rickcox/Hepta-Pi/3V3_to_2v5_PSU.kicad_sch

## KiCad design 3V3_to_2v5_PSU.kicad_sch (2023-05-14)

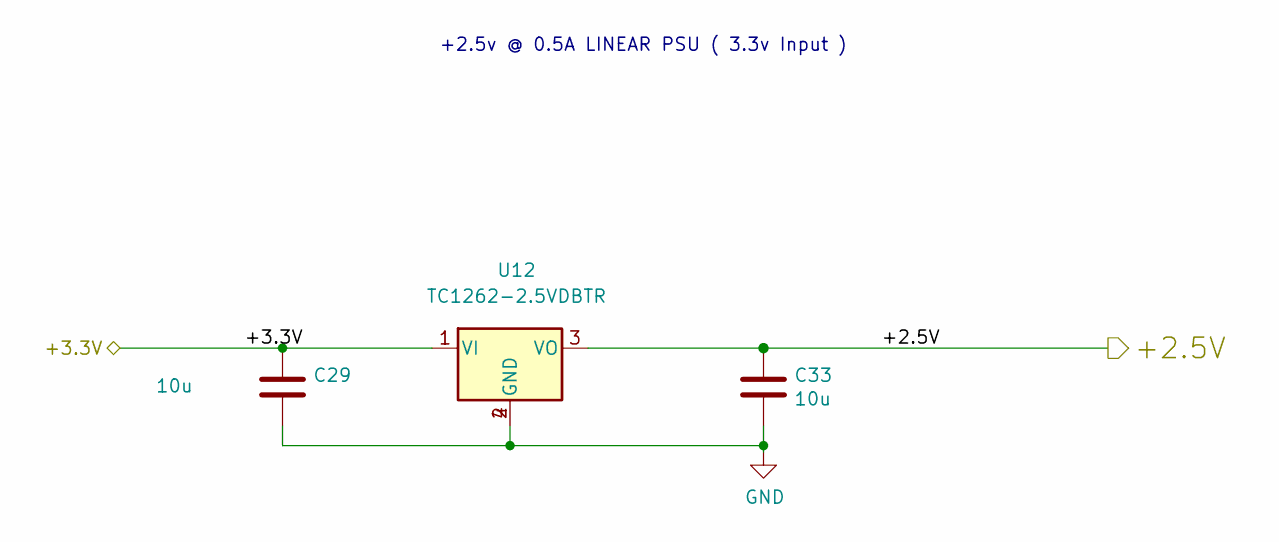
[picture p10: schematic 3V3_to_2v5_PSU.kicad_sch]

Parts:
C29, C33: 10u; C_0603_1608Metric; Part Description CAP CER 10UF 6.3V X5R 0603; LCSC Part Number C19702
U12: TC1262-2.5VDBTR; SOT-223; Manuf Partno TC1262-2.5VDBTR; LCSC Part Number C233212

Connections:
+2.5V: C33.1, U12.3 (VO)
+3.3V: C29.1, U12.1 (VI)
GND: C29.2, C33.2, U12.2 (GND), U12.4

Notes on the sheet:
+2.5v @ 0.5A LINEAR PSU ( 3.3v Input )
