rickcox/Hepta-Pi/12V_to_1v0_PSU.kicad_sch

## KiCad design 12V_to_1v0_PSU.kicad_sch (2023-05-14)

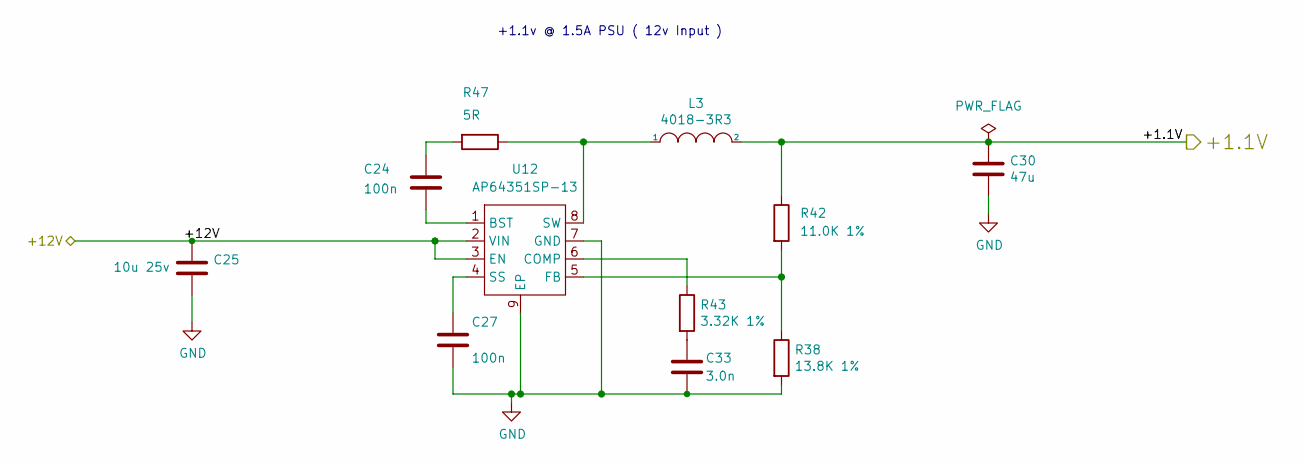
[picture p11: schematic 12V_to_1v0_PSU.kicad_sch]

Parts:
C24, C27: 100n; C_0402_1005Metric; LCSC Part Number C1525
C25: 10u 25v; C_0805_2012Metric; LCSC Part Number C440198
C30: 47u; C_1206_3216Metric; LCSC Part Number C96123
C33: 3.0n; C_0603_1608Metric; LCSC Part Number C1613
L3: 4018-3R3; L_Bourns-SRN4018; LCSC Part Number C307830
R38: 13.8K 1%; R_0603_1608Metric; LCSC Part Number C862888
R42: 11.0K 1%; R_0603_1608Metric; LCSC Part Number C25950
R43: 3.32K 1%; R_0603_1608Metric; LCSC Part Number C22995
R47: 5R; R_0603_1608Metric; LCSC Part Number C25197
U12: AP64351SP-13; SOIC-8-1EP_3.9x4.9mm_P1.27mm_EP2.95x4.9mm_Mask2.71x3.4mm

Connections:
+1.1V: C30.1, L3.2, R42.1
+12V: C25.1, U12.2 (VIN), U12.3 (EN)
GND: C25.2, C27.2, C30.2, C33.2, R38.2, U12.7 (GND), U12.9 (EP)
unnamed: C24.1, R47.2
unnamed: C24.2, U12.1 (BST)
unnamed: C27.1, U12.4 (SS)
unnamed: C33.1, R43.2
unnamed: L3.1, R47.1, U12.8 (SW)
unnamed: R38.1, R42.2, U12.5 (FB)
unnamed: R43.1, U12.6 (COMP)

Notes on the sheet:
+1.1v @ 1.5A PSU ( 12v Input )
