rickcox/Hepta-Pi/12V_to_1v2_PSU.kicad_sch

## KiCad design 12V_to_1v2_PSU.kicad_sch (2023-05-14)

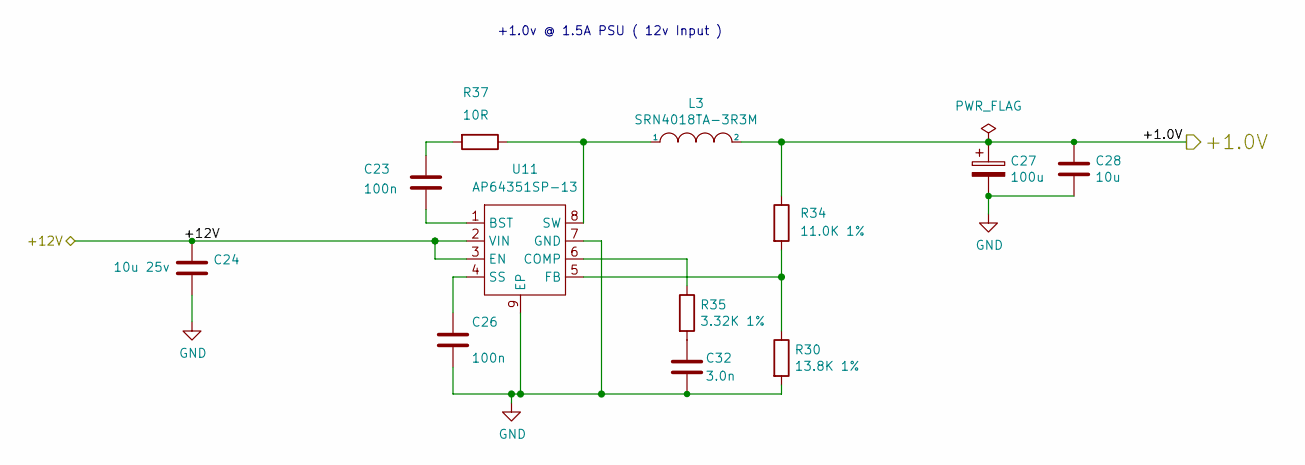
[picture p12: schematic 12V_to_1v2_PSU.kicad_sch]

Parts:
C23, C26: 100n; C_0402_1005Metric; Part Description CAP CER 0.1UF 6.3V X5R 0603; LCSC Part Number C1525
C24: 10u 25v; C_0805_2012Metric; Part Description CAP CER 10UF 25V X5R 0805; LCSC Part Number C440198
C27: 100u; CP_EIA-3528-21_Kemet-B; Part Description CAP TANT 100UF 10% 10V 2917; LCSC Part Number C16133
C28: 10u; C_0603_1608Metric; Part Description CAP CER 10UF 6.3V X5R 0603; LCSC Part Number C19702
C32: 3.0n; C_0603_1608Metric; Part Description CAP CER 0603 3NF 16V; LCSC Part Number C1613
L3: SRN4018TA-3R3M; L_Bourns-SRN4018; Part Description Power Inductor (SMD), 3.3 µH, 2.0 A, Se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; LCSC Part Number C307830
R30: 13.8K 1%; R_0603_1608Metric; Part Description RES 22.1K OHM 1% 1/10W 0603; LCSC Part Number C25961
R34: 11.0K 1%; R_0603_1608Metric; Part Description RES 11K OHM 1% 1/10W 0603; LCSC Part Number C25950
R35: 3.32K 1%; R_0603_1608Metric; Part Description RES 3.32K OHM 1% 1/10W 0603; LCSC Part Number C22995
R37: 10R; R_0603_1608Metric; Part Description RES 10 OHM 1% 1/10W 0603; LCSC Part Number C22859
U11: AP64351SP-13; SOIC-8-1EP_3.9x4.9mm_P1.27mm_EP2.95x4.9mm_Mask2.71x3.4mm; Manuf Partno AP64351SP-13

Connections:
+1.0V: C27.1, C28.1, L3.2, R34.1
+12V: C24.1, U11.2 (VIN), U11.3 (EN)
GND: C24.2, C26.2, C27.2, C28.2, C32.2, R30.2, U11.7 (GND), U11.9 (EP)
unnamed: C23.1, R37.2
unnamed: C23.2, U11.1 (BST)
unnamed: C26.1, U11.4 (SS)
unnamed: C32.1, R35.2
unnamed: L3.1, R37.1, U11.8 (SW)
unnamed: R30.1, R34.2, U11.5 (FB)
unnamed: R35.1, U11.6 (COMP)

Notes on the sheet:
+1.0v @ 1.5A PSU ( 12v Input )
