rickcox/Hepta-Pi/12V_to_5v_2_PSU.kicad_sch

## KiCad design 12V_to_5v_2_PSU.kicad_sch (2023-05-14)

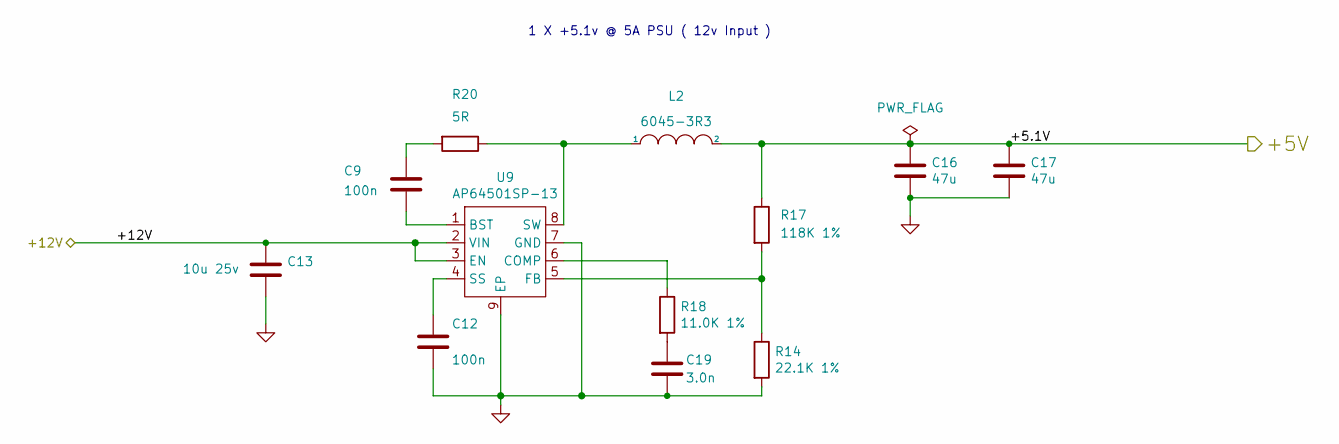
[picture p13: schematic 12V_to_5v_2_PSU.kicad_sch]

Parts:
C9, C12: 100n; C_0603_1608Metric; LCSC Part Number C14663
C13: 10u 25v; C_0805_2012Metric; LCSC Part Number C440198
C16, C17: 47u; C_1206_3216Metric; LCSC Part Number C96123
C19: 3.0n; C_0603_1608Metric; LCSC Part Number C1613
L2: 6045-3R3; L_Bourns_SRN6045TA; Part Description 3.3uH ±20% 5.5AMP SMD,6x6x4.5mm Power I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; LCSC Part Number C135301
R14: 22.1K 1%; R_0603_1608Metric; LCSC Part Number C25961
R17: 118K 1%; R_0603_1608Metric; LCSC Part Number C25806
R18: 11.0K 1%; R_0603_1608Metric; LCSC Part Number C25950
R20: 5R; R_0603_1608Metric; LCSC Part Number C25197
U9: AP64501SP-13; SOIC-8-1EP_3.9x4.9mm_P1.27mm_EP2.95x4.9mm_Mask2.71x3.4mm; LCSC Part Number C2071517

Connections:
+5.1V: C16.1, C17.1, L2.2, R17.1
+12V: C13.1, U9.2 (VIN), U9.3 (EN)
unnamed: C9.1, R20.2
unnamed: C9.2, U9.1 (BST)
unnamed: C12.1, U9.4 (SS)
unnamed: C19.1, R18.2
unnamed: L2.1, R20.1, U9.8 (SW)
unnamed: R14.1, R17.2, U9.5 (FB)
unnamed: R18.1, U9.6 (COMP)
~: C12.2, C13.2, C16.2, C17.2, C19.2, R14.2, U9.7 (GND), U9.9 (EP)

Notes on the sheet:
1 X +5.1v @ 5A PSU ( 12v Input )
