rickcox/Hepta-Pi/12v_to_3v3_PSU.kicad_sch

## KiCad design 12v_to_3v3_PSU.kicad_sch (2023-05-14)

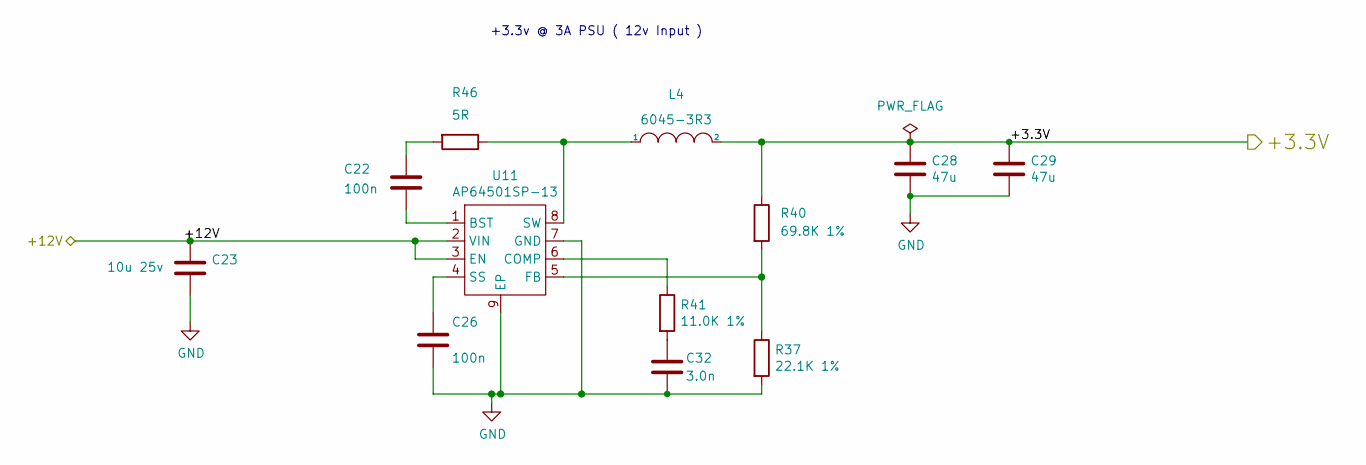
[picture p14: schematic 12v_to_3v3_PSU.kicad_sch]

Parts:
C22, C26: 100n; C_0402_1005Metric; LCSC Part Number C1525
C23: 10u 25v; C_0805_2012Metric; LCSC Part Number C440198
C28, C29: 47u; C_1206_3216Metric; LCSC Part Number C96123
C32: 3.0n; C_0603_1608Metric; LCSC Part Number C1613
L4: 6045-3R3; L_Bourns_SRN6045TA; Part Description 3.3uH ±20% 5.5AMP SMD,6x6x4.5mm Power I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; LCSC Part Number C135301
R37: 22.1K 1%; R_0603_1608Metric; LCSC Part Number C25961
R40: 69.8K 1%; R_0603_1608Metric; LCSC Part Number C23098
R41: 11.0K 1%; R_0603_1608Metric; LCSC Part Number C25950
R46: 5R; R_0603_1608Metric; LCSC Part Number C25197
U11: AP64501SP-13; SOIC-8-1EP_3.9x4.9mm_P1.27mm_EP2.95x4.9mm_Mask2.71x3.4mm; LCSC Part Number C2071517

Connections:
+3.3V: C28.1, C29.1, L4.2, R40.1
+12V: C23.1, U11.2 (VIN), U11.3 (EN)
GND: C23.2, C26.2, C28.2, C29.2, C32.2, R37.2, U11.7 (GND), U11.9 (EP)
unnamed: C22.1, R46.2
unnamed: C22.2, U11.1 (BST)
unnamed: C26.1, U11.4 (SS)
unnamed: C32.1, R41.2
unnamed: L4.1, R46.1, U11.8 (SW)
unnamed: R37.1, R40.2, U11.5 (FB)
unnamed: R41.1, U11.6 (COMP)

Notes on the sheet:
+3.3v @ 3A PSU ( 12v Input )
