rickcox/Hepta-Pi/CM4_GPIO.kicad_sch

## KiCad design CM4_GPIO.kicad_sch (2023-05-14)

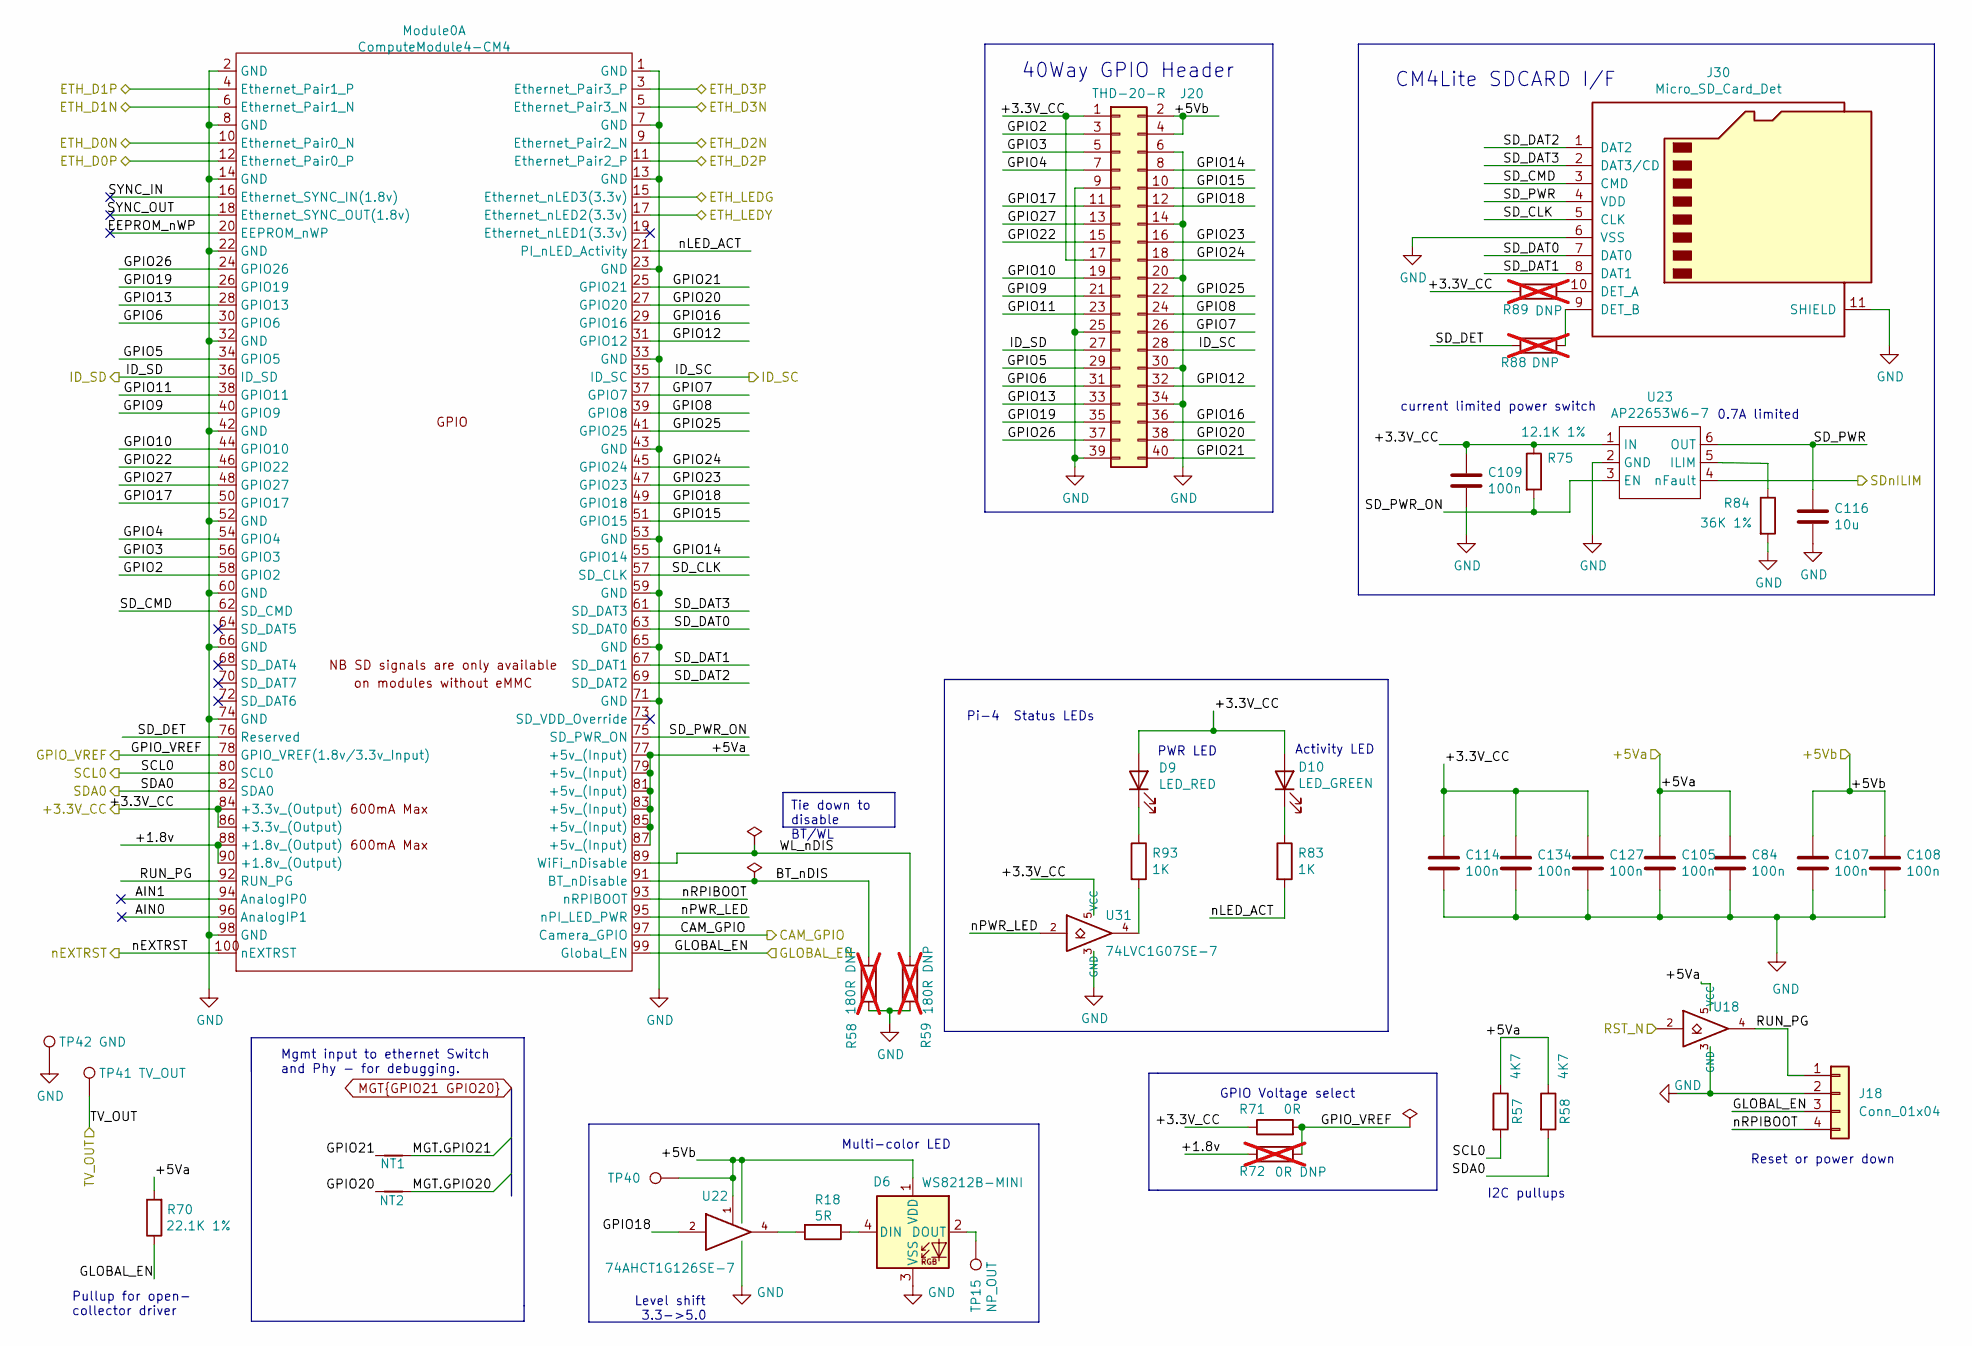
[picture p15: schematic CM4_GPIO.kicad_sch]

Parts:
C84, C105, C107, C108, C109, C114, C127, C134: 100n; C_0402_1005Metric; LCSC Part Number C1525
C116: 10u; C_0603_1608Metric; LCSC Part Number C19702
D6: WS8212B-MINI; LED_SK6812MINI_PLCC4_3.5x3.5mm_P1.75mm; LCSC Part Number C527089
D9: LED_RED; LED_0805_2012Metric_Pad1.15x1.40mm_HandSolder; LCSC Part Number C84256
D10: LED_GREEN; LED_0805_2012Metric_Pad1.15x1.40mm_HandSolder; LCSC Part Number C2297
J18: Conn_01x04; PinHeader_1x04_P2.54mm_Vertical
J20: THD-20-R; PinHeader_2x20_P2.54mm_Vertical; Part Description 2X20 0.1in pin header
J30: Micro_SD_Card_Det; SDCARD_MOLEX_503398-1892; LCSC Part Number C428492
Module0: ComputeModule4-CM4; Raspberry-Pi-4-Compute-Module
NT1, NT2: NetTie_2; NetTie-2_SMD_Pad0.5mm; LCSC Part Number DNP
R18: 5R; R_0603_1608Metric; LCSC Part Number C25197
R57, R58: 4K7; R_0603_1608Metric; LCSC Part Number C99782
R59: 180R DNP; R_0603_1608Metric_Pad0.98x0.95mm_HandSolder; LCSC Part Number DNP; not fitted
R70: 22.1K 1%; R_0603_1608Metric; LCSC Part Number C25961
R71: 0R; R_0603_1608Metric; LCSC Part Number C21189
R72: 0R DNP; R_0603_1608Metric_Pad0.98x0.95mm_HandSolder; LCSC Part Number C21189; not fitted
R75: 12.1K 1%; R_0603_1608Metric; LCSC Part Number C22864
R83, R93: 1K; R_0603_1608Metric; LCSC Part Number C21190
R84: 36K 1%; R_0603_1608Metric; LCSC Part Number C23147
R88, R89: DNP; R_0603_1608Metric_Pad0.98x0.95mm_HandSolder; LCSC Part Number DNP; not fitted
TP15: NP_OUT; TestPoint_Pad_D1.0mm; LCSC Part Number DNP
TP40: +5; TestPoint_Pad_D1.0mm; LCSC Part Number DNP
TP41: TV_OUT; TestPoint_Pad_D1.0mm; LCSC Part Number DNP
TP42: GND; TestPoint_Pad_D1.0mm; LCSC Part Number DNP
U18, U31: 74LVC1G07SE-7; SOT-353_SC-70-5; LCSC Part Number C67531
U22: 74AHCT1G126SE-7; SOT-353_SC-70-5; LCSC Part Number C150723
U23: AP22653W6-7; SOT-23-6; LCSC Part Number C2158037

Connections:
+1.8v: Module0.88 (+1.8v_(Output)), Module0.90 (+1.8v_(Output)), R72.1
+3.3V_CC: C109.1, C114.1, C127.1, C134.1, D9.2 (A), D10.2 (A), J20.1, J20.17, Module0.84 (+3.3v_(Output)), Module0.86 (+3.3v_(Output)), R71.1, R75.1, R89.1, U23.1 (IN), U31.5 (VCC)
+5Va: C84.1, C105.1, Module0.77 (+5v_(Input)), Module0.79 (+5v_(Input)), Module0.81 (+5v_(Input)), Module0.83 (+5v_(Input)), Module0.85 (+5v_(Input)), Module0.87 (+5v_(Input)), R57.1, R58.1, R70.2, U18.5 (VCC)
+5Vb: C107.1, C108.1, D6.1 (VDD), J20.2, J20.4, TP40.1, U22.1, U22.5 (VCC)
AIN0: Module0.96 (AnalogIP1)
AIN1: Module0.94 (AnalogIP0)
BT_nDIS: Module0.91 (BT_nDisable), R58.2
CAM_GPIO: Module0.97 (Camera_GPIO)
EEPROM_nWP: Module0.20 (EEPROM_nWP)
ETH_D0N: Module0.10 (Ethernet_Pair0_N)
ETH_D0P: Module0.12 (Ethernet_Pair0_P)
ETH_D1N: Module0.6 (Ethernet_Pair1_N)
ETH_D1P: Module0.4 (Ethernet_Pair1_P)
ETH_D2N: Module0.9 (Ethernet_Pair2_N)
ETH_D2P: Module0.11 (Ethernet_Pair2_P)
ETH_D3N: Module0.5 (Ethernet_Pair3_N)
ETH_D3P: Module0.3 (Ethernet_Pair3_P)
ETH_LEDG: Module0.15 (Ethernet_nLED3(3.3v))
ETH_LEDY: Module0.17 (Ethernet_nLED2(3.3v))
GLOBAL_EN: J18.3, Module0.99 (Global_EN), R70.1
GND: C84.2, C105.2, C107.2, C108.2, C109.2, C114.2, C116.2, C127.2, C134.2, D6.3 (VSS), J18.2, J20.6, J20.9, J20.14, J20.20, J20.25, J20.30, J20.34, J20.39, J30.6 (VSS), J30.11 (SHIELD), Module0.1 (GND), Module0.2 (GND), Module0.7 (GND), Module0.8 (GND), Module0.13 (GND), Module0.14 (GND), Module0.22 (GND), Module0.23 (GND), Module0.32 (GND), Module0.33 (GND), Module0.42 (GND), Module0.43 (GND), Module0.52 (GND), Module0.53 (GND), Module0.59 (GND), Module0.60 (GND), Module0.65 (GND), Module0.66 (GND), Module0.71 (GND), Module0.74 (GND), Module0.98 (GND), R58.1, R59.1, R84.2, TP42.1, U18.3 (GND), U22.3 (GND), U23.2 (GND), U31.3 (GND)
GPIO2: J20.3, Module0.58 (GPIO2)
GPIO3: J20.5, Module0.56 (GPIO3)
GPIO4: J20.7, Module0.54 (GPIO4)
GPIO5: J20.29, Module0.34 (GPIO5)
GPIO6: J20.31, Module0.30 (GPIO6)
GPIO7: J20.26, Module0.37 (GPIO7)
GPIO8: J20.24, Module0.39 (GPIO8)
GPIO9: J20.21, Module0.40 (GPIO9)
GPIO10: J20.19, Module0.44 (GPIO10)
GPIO11: J20.23, Module0.38 (GPIO11)
GPIO12: J20.32, Module0.31 (GPIO12)
GPIO13: J20.33, Module0.28 (GPIO13)
GPIO14: J20.8, Module0.55 (GPIO14)
GPIO15: J20.10, Module0.51 (GPIO15)
GPIO16: J20.36, Module0.29 (GPIO16)
GPIO17: J20.11, Module0.50 (GPIO17)
GPIO18: J20.12, Module0.49 (GPIO18), U22.2
GPIO19: J20.35, Module0.26 (GPIO19)
GPIO20: J20.38, Module0.27 (GPIO20), NT2.1
GPIO21: J20.40, Module0.25 (GPIO21), NT1.1
GPIO22: J20.15, Module0.46 (GPIO22)
GPIO23: J20.16, Module0.47 (GPIO23)
GPIO24: J20.18, Module0.45 (GPIO24)
GPIO25: J20.22, Module0.41 (GPIO25)
GPIO26: J20.37, Module0.24 (GPIO26)
GPIO27: J20.13, Module0.48 (GPIO27)
GPIO_VREF: Module0.78 (GPIO_VREF(1.8v/3.3v_Input)), R71.2, R72.2
ID_SC: J20.28, Module0.35 (ID_SC)
ID_SD: J20.27, Module0.36 (ID_SD)
MGT.GPIO20: NT2.2
MGT.GPIO21: NT1.2
unnamed: D6.2 (DOUT), TP15.1
unnamed: D6.4 (DIN), R18.1
unnamed: D9.1 (K), R93.1
unnamed: D10.1 (K), R83.1
unnamed: J30.9 (DET_B), R88.2
unnamed: J30.10 (DET_A), R89.2
unnamed: R18.2, U22.4
unnamed: R84.1, U23.5 (ILIM)
unnamed: R93.2, U31.4
RST_N: U18.2
RUN_PG: J18.1, Module0.92 (RUN_PG), U18.4
SCL0: Module0.80 (SCL0), R57.2
SDA0: Module0.82 (SDA0), R58.2
SD_CLK: J30.5 (CLK), Module0.57 (SD_CLK)
SD_CMD: J30.3 (CMD), Module0.62 (SD_CMD)
SD_DAT0: J30.7 (DAT0), Module0.63 (SD_DAT0)
SD_DAT1: J30.8 (DAT1), Module0.67 (SD_DAT1)
SD_DAT2: J30.1 (DAT2), Module0.69 (SD_DAT2)
SD_DAT3: J30.2 (DAT3/CD), Module0.61 (SD_DAT3)
SD_DET: Module0.76 (Reserved), R88.1
SD_PWR: C116.1, J30.4 (VDD), U23.6 (OUT)
SD_PWR_ON: Module0.75 (SD_PWR_ON), R75.2, U23.3 (EN)
SDnILIM: U23.4 (nFault)
SYNC_IN: Module0.16 (Ethernet_SYNC_IN(1.8v))
SYNC_OUT: Module0.18 (Ethernet_SYNC_OUT(1.8v))
TV_OUT: TP41.1
WL_nDIS: Module0.89 (WiFi_nDisable), R59.2
nEXTRST: Module0.100 (nEXTRST)
nLED_ACT: Module0.21 (PI_nLED_Activity), R83.2
nPWR_LED: Module0.95 (nPI_LED_PWR), U31.2
nRPIBOOT: J18.4, Module0.93 (nRPIBOOT)

Notes on the sheet:
Tie down to disable BT/WL
I2C pullups
40Way GPIO Header
0.7A limited
Pi-4 Status LEDs
CM4Lite SDCARD I/F
Pullup for open- collector driver
Level shift 3.3->5.0
Multi-color LED
GPIO Voltage select
Reset or power down
PWR LED
Mgmt input to ethernet Switch and Phy - for debugging.
current limited power switch
Activity LED
