rickcox/Hepta-Pi/CM4_HighSpeed.kicad_sch

## KiCad design CM4_HighSpeed.kicad_sch (2023-05-14)

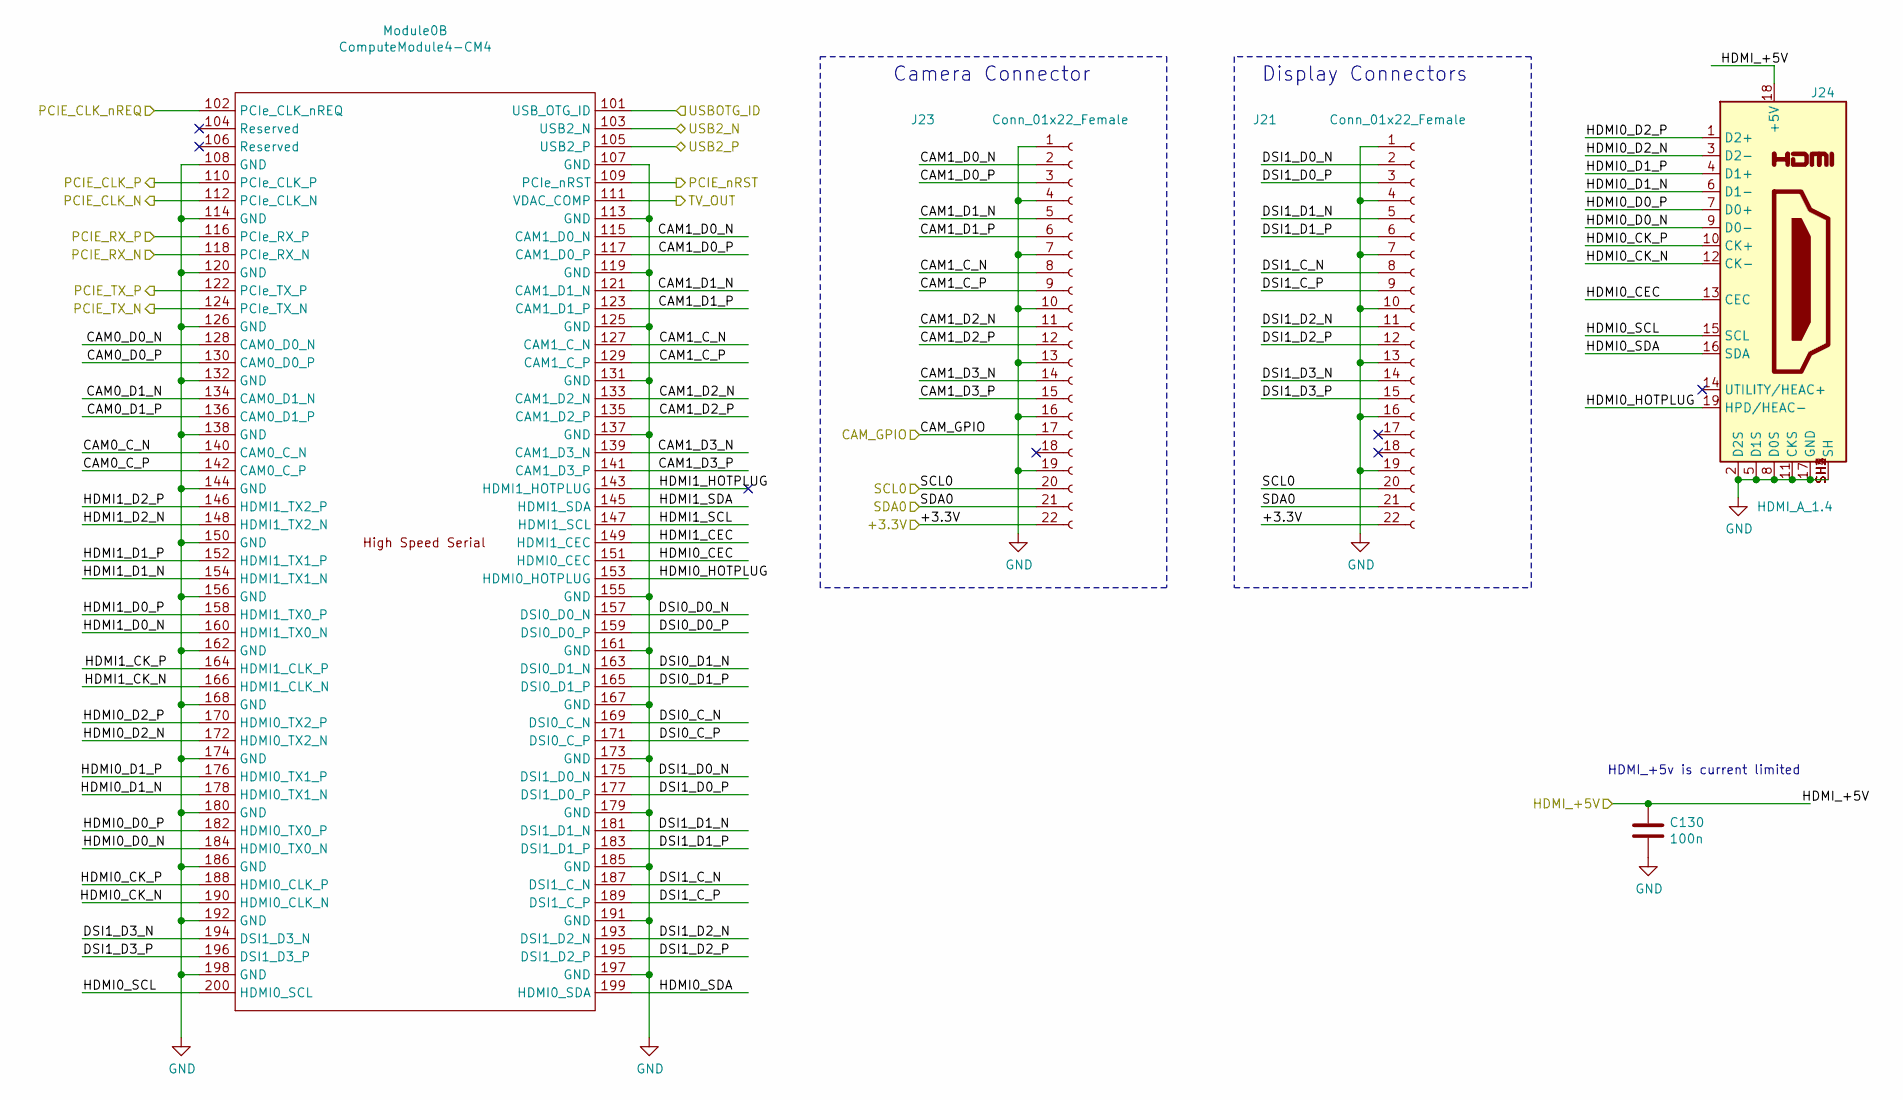
[picture p16: schematic CM4_HighSpeed.kicad_sch]

Parts:
C130: 100n; C_0402_1005Metric; LCSC Part Number C1525
J21, J23: Conn_01x22_Female; Hirose_FH12-22S-0.5SV55_P0.5mm_Vertical; Part Description 22 Contact Surface Mount 0.5mm SMD,P=0.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
J24: HDMI_A_1.4; EDAC 690-019-298-412; LCSC Part Number C720616
Module0: ComputeModule4-CM4; Raspberry-Pi-4-Compute-Module

Connections:
+3.3V: J21.22, J23.22
CAM0_C_N: Module0.140 (CAM0_C_N)
CAM0_C_P: Module0.142 (CAM0_C_P)
CAM0_D0_N: Module0.128 (CAM0_D0_N)
CAM0_D0_P: Module0.130 (CAM0_D0_P)
CAM0_D1_N: Module0.134 (CAM0_D1_N)
CAM0_D1_P: Module0.136 (CAM0_D1_P)
CAM1_C_N: J23.8, Module0.127 (CAM1_C_N)
CAM1_C_P: J23.9, Module0.129 (CAM1_C_P)
CAM1_D0_N: J23.2, Module0.115 (CAM1_D0_N)
CAM1_D0_P: J23.3, Module0.117 (CAM1_D0_P)
CAM1_D1_N: J23.5, Module0.121 (CAM1_D1_N)
CAM1_D1_P: J23.6, Module0.123 (CAM1_D1_P)
CAM1_D2_N: J23.11, Module0.133 (CAM1_D2_N)
CAM1_D2_P: J23.12, Module0.135 (CAM1_D2_P)
CAM1_D3_N: J23.14, Module0.139 (CAM1_D3_N)
CAM1_D3_P: J23.15, Module0.141 (CAM1_D3_P)
CAM_GPIO: J23.17
DSI0_C_N: Module0.169 (DSI0_C_N)
DSI0_C_P: Module0.171 (DSI0_C_P)
DSI0_D0_N: Module0.157 (DSI0_D0_N)
DSI0_D0_P: Module0.159 (DSI0_D0_P)
DSI0_D1_N: Module0.163 (DSI0_D1_N)
DSI0_D1_P: Module0.165 (DSI0_D1_P)
DSI1_C_N: J21.8, Module0.187 (DSI1_C_N)
DSI1_C_P: J21.9, Module0.189 (DSI1_C_P)
DSI1_D0_N: J21.2, Module0.175 (DSI1_D0_N)
DSI1_D0_P: J21.3, Module0.177 (DSI1_D0_P)
DSI1_D1_N: J21.5, Module0.181 (DSI1_D1_N)
DSI1_D1_P: J21.6, Module0.183 (DSI1_D1_P)
DSI1_D2_N: J21.11, Module0.193 (DSI1_D2_N)
DSI1_D2_P: J21.12, Module0.195 (DSI1_D2_P)
DSI1_D3_N: J21.14, Module0.194 (DSI1_D3_N)
DSI1_D3_P: J21.15, Module0.196 (DSI1_D3_P)
GND: C130.2, J21.1, J21.4, J21.7, J21.10, J21.13, J21.16, J21.19, J23.1, J23.4, J23.7, J23.10, J23.13, J23.16, J23.19, J24.2 (D2S), J24.5 (D1S), J24.8 (D0S), J24.11 (CKS), J24.17 (GND), J24.SH1 (SH), J24.SH2 (SH), J24.SH3 (SH), J24.SH4 (SH), Module0.107 (GND), Module0.108 (GND), Module0.113 (GND), Module0.114 (GND), Module0.119 (GND), Module0.120 (GND), Module0.125 (GND), Module0.126 (GND), Module0.131 (GND), Module0.132 (GND), Module0.137 (GND), Module0.138 (GND), Module0.144 (GND), Module0.150 (GND), Module0.155 (GND), Module0.156 (GND), Module0.161 (GND), Module0.162 (GND), Module0.167 (GND), Module0.168 (GND), Module0.173 (GND), Module0.174 (GND), Module0.179 (GND), Module0.180 (GND), Module0.185 (GND), Module0.186 (GND), Module0.191 (GND), Module0.192 (GND), Module0.197 (GND), Module0.198 (GND)
HDMI0_CEC: J24.13 (CEC), Module0.151 (HDMI0_CEC)
HDMI0_CK_N: J24.12 (CK-), Module0.190 (HDMI0_CLK_N)
HDMI0_CK_P: J24.10 (CK+), Module0.188 (HDMI0_CLK_P)
HDMI0_D0_N: J24.9 (D0-), Module0.184 (HDMI0_TX0_N)
HDMI0_D0_P: J24.7 (D0+), Module0.182 (HDMI0_TX0_P)
HDMI0_D1_N: J24.6 (D1-), Module0.178 (HDMI0_TX1_N)
HDMI0_D1_P: J24.4 (D1+), Module0.176 (HDMI0_TX1_P)
HDMI0_D2_N: J24.3 (D2-), Module0.172 (HDMI0_TX2_N)
HDMI0_D2_P: J24.1 (D2+), Module0.170 (HDMI0_TX2_P)
HDMI0_HOTPLUG: J24.19 (HPD/HEAC-), Module0.153 (HDMI0_HOTPLUG)
HDMI0_SCL: J24.15 (SCL), Module0.200 (HDMI0_SCL)
HDMI0_SDA: J24.16 (SDA), Module0.199 (HDMI0_SDA)
HDMI1_CEC: Module0.149 (HDMI1_CEC)
HDMI1_CK_N: Module0.166 (HDMI1_CLK_N)
HDMI1_CK_P: Module0.164 (HDMI1_CLK_P)
HDMI1_D0_N: Module0.160 (HDMI1_TX0_N)
HDMI1_D0_P: Module0.158 (HDMI1_TX0_P)
HDMI1_D1_N: Module0.154 (HDMI1_TX1_N)
HDMI1_D1_P: Module0.152 (HDMI1_TX1_P)
HDMI1_D2_N: Module0.148 (HDMI1_TX2_N)
HDMI1_D2_P: Module0.146 (HDMI1_TX2_P)
HDMI1_HOTPLUG: Module0.143 (HDMI1_HOTPLUG)
HDMI1_SCL: Module0.147 (HDMI1_SCL)
HDMI1_SDA: Module0.145 (HDMI1_SDA)
HDMI_+5V: C130.1, J24.18 (+5V)
PCIE_CLK_N: Module0.112 (PCIe_CLK_N)
PCIE_CLK_P: Module0.110 (PCIe_CLK_P)
PCIE_CLK_nREQ: Module0.102 (PCIe_CLK_nREQ)
PCIE_RX_N: Module0.118 (PCIe_RX_N)
PCIE_RX_P: Module0.116 (PCIe_RX_P)
PCIE_TX_N: Module0.124 (PCIe_TX_N)
PCIE_TX_P: Module0.122 (PCIe_TX_P)
PCIE_nRST: Module0.109 (PCIe_nRST)
SCL0: J21.20, J23.20
SDA0: J21.21, J23.21
TV_OUT: Module0.111 (VDAC_COMP)
USB2_N: Module0.103 (USB2_N)
USB2_P: Module0.105 (USB2_P)
USBOTG_ID: Module0.101 (USB_OTG_ID)

Notes on the sheet:
Display Connectors
HDMI_+5v is current limited
Camera Connector
