rickcox/Hepta-Pi/Hepta-Pi_1.1.kicad_sch

## KiCad design Hepta-Pi_1.1.kicad_sch (2023-05-14)

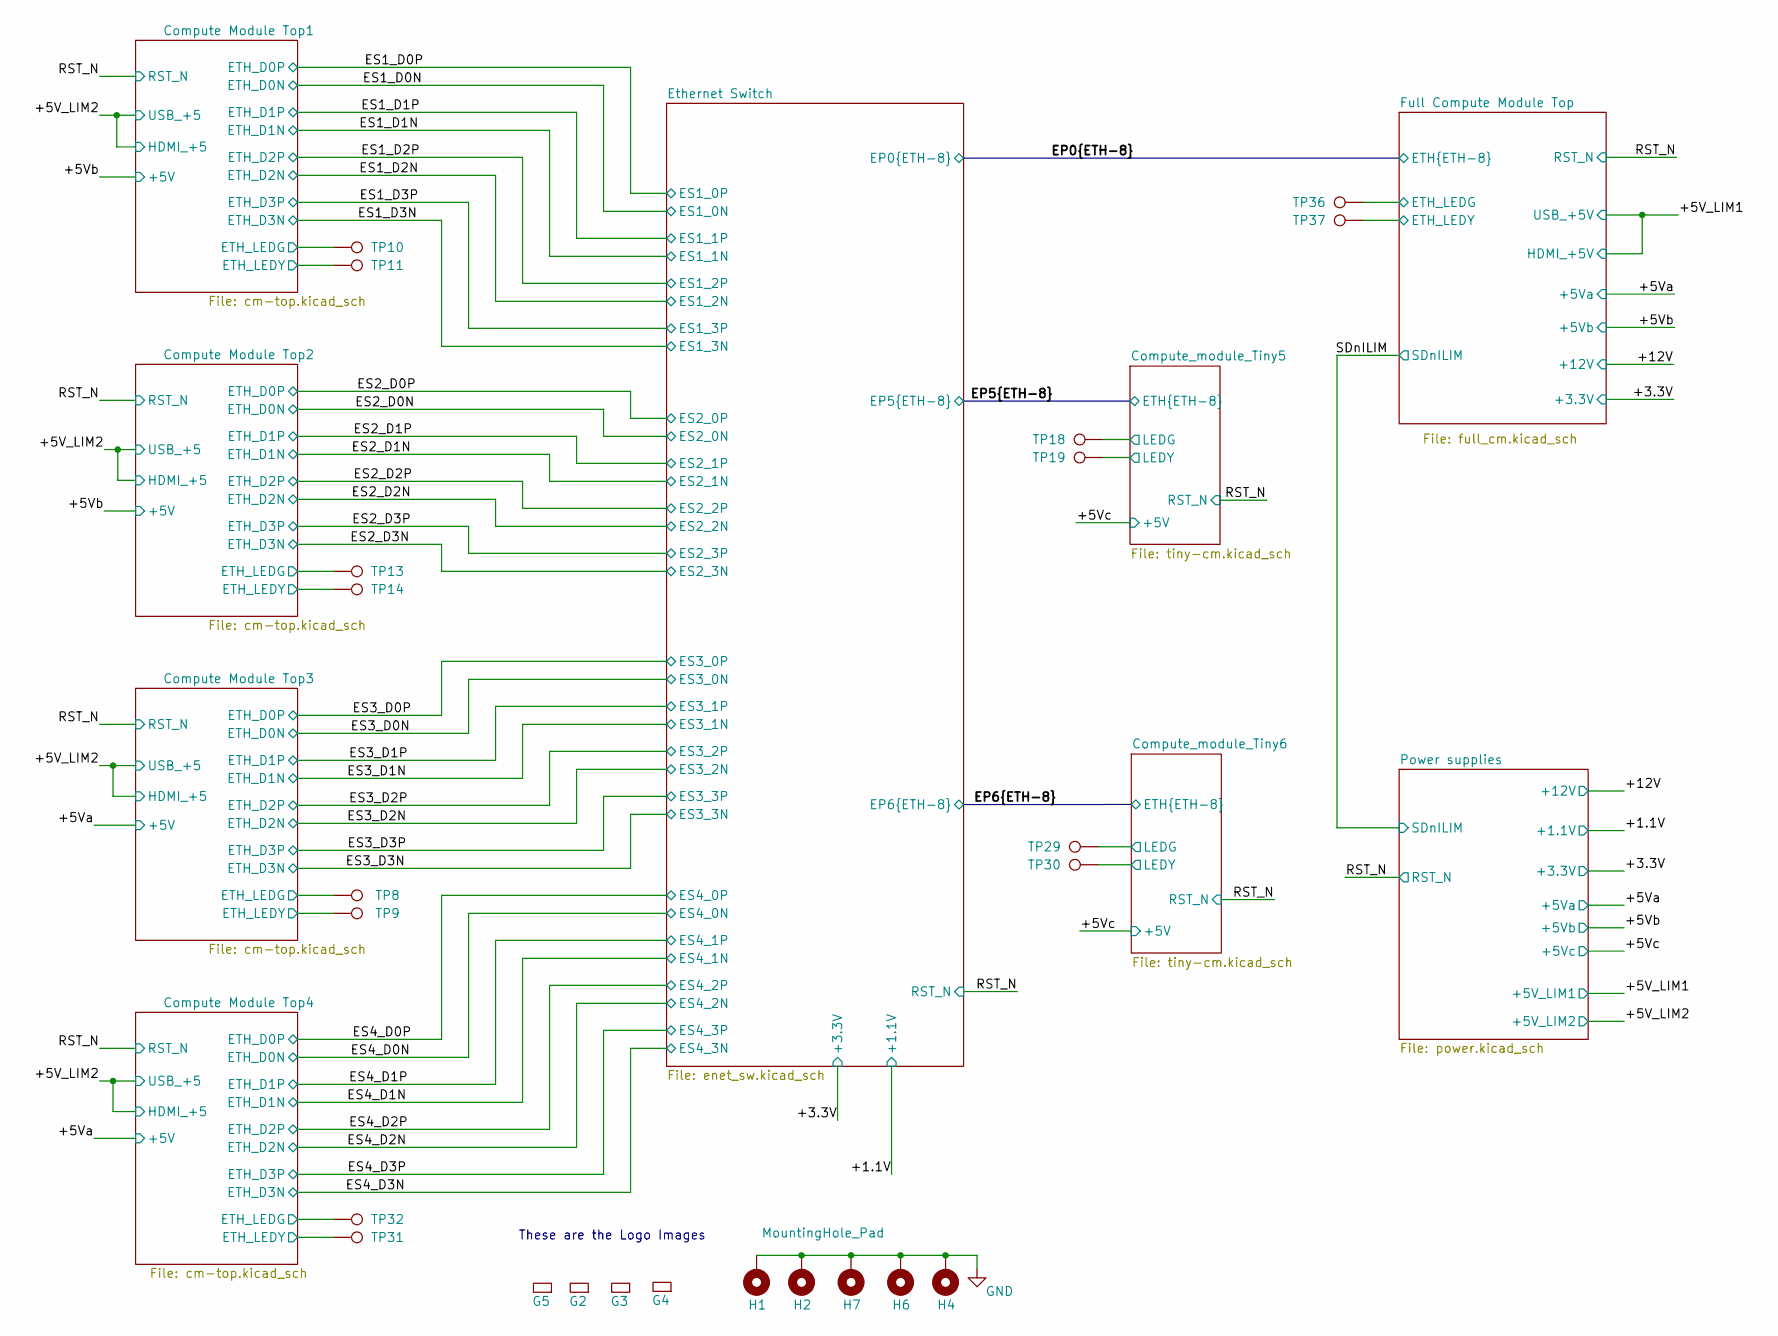
[picture p17: schematic Hepta-Pi_1.1.kicad_sch]

Parts:
G2, G5: coxyz; KiCad-Logo2_6mm_SilkScreen; LCSC Part Number DNP
G3, G4: coxyz; LCSC Part Number DNP
H1, H2, H4, H6, H7: MountingHole_Pad; MountingHole_3.2mm_M3_Pad_TopBottom; LCSC Part Number DNP
TP8, TP9, TP10, TP11, TP13, TP14, TP18, TP19, TP29, TP30, TP31, TP32, TP36, TP37: TestPoint; TestPoint_Pad_D1.0mm; LCSC Part Number DNP

Connections:
ETH_LEDG: TP8.1, TP10.1, TP13.1, TP32.1, TP36.1
ETH_LEDY: TP9.1, TP11.1, TP14.1, TP31.1, TP37.1
GND: H1.1, H2.1, H4.1, H6.1, H7.1
LEDG: TP18.1, TP29.1
LEDY: TP19.1, TP30.1

Notes on the sheet:
These are the Logo Images
