rickcox/Hepta-Pi/M2-routing.kicad_sch

## KiCad design M2-routing.kicad_sch (2023-05-14)

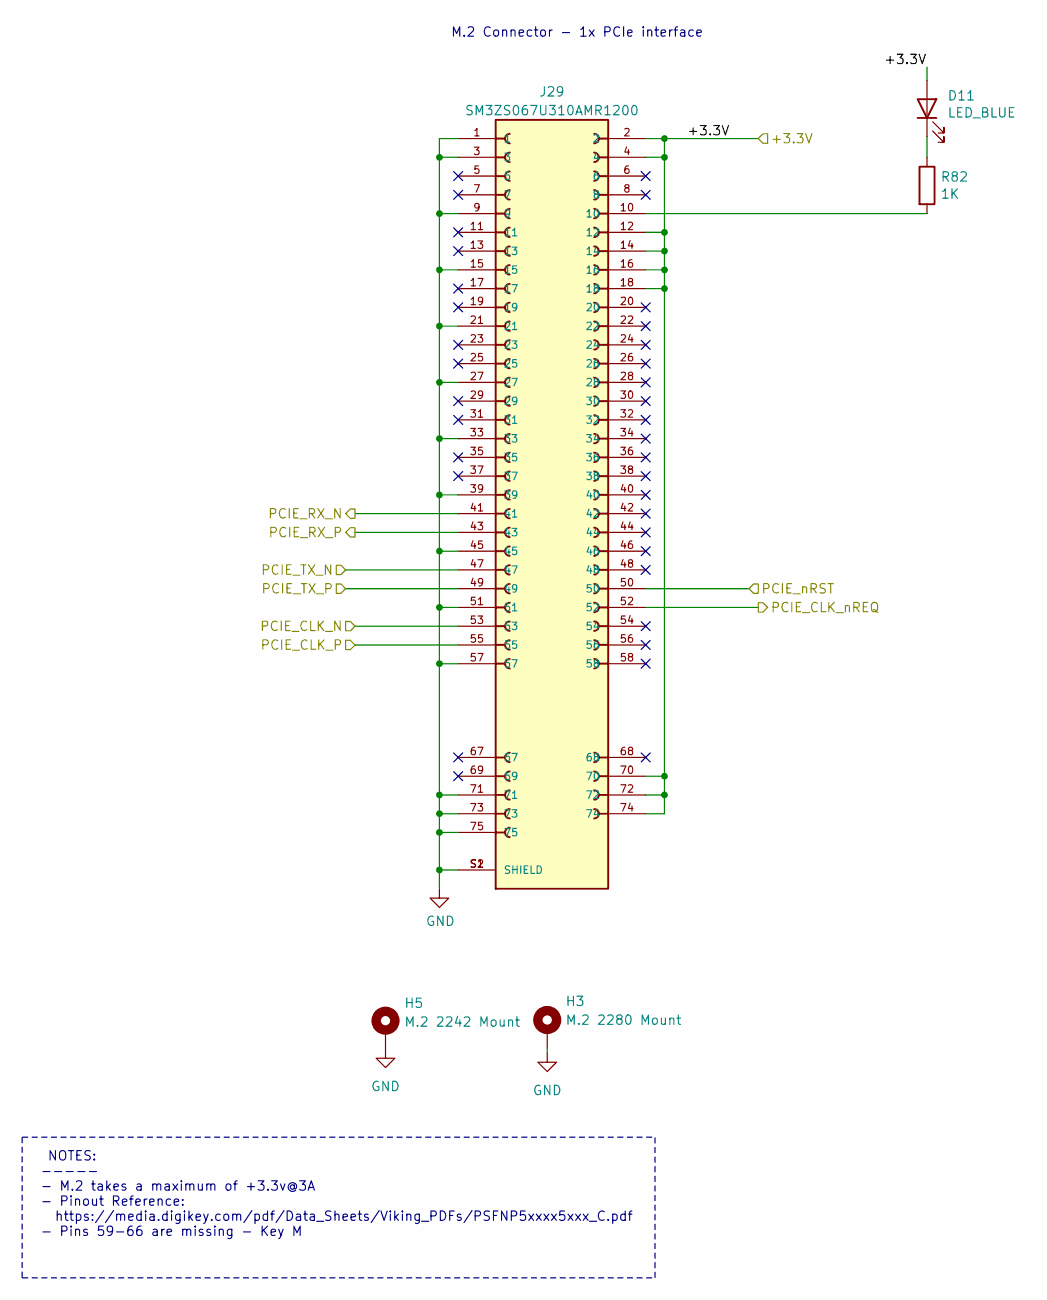
[picture p18: schematic M2-routing.kicad_sch]

Parts:
D11: LED_BLUE; LED_0805_2012Metric_Pad1.15x1.40mm_HandSolder; LCSC Part Number C99870
H3: M.2 2280 Mount; M.2_Standoff; Manuf Partno SM3ZS067U310-NUT1
H5: M.2 2242 Mount; M.2_Standoff; Manuf Partno SM3ZS067U310-NUT1
J29: SM3ZS067U310AMR1200; JAE_SM3ZS067U310AMR1200; Part Description M.2 Key M connector; LCSC Part Number C4527433
R82: 1K; R_0603_1608Metric; LCSC Part Number C21190

Connections:
+3.3V: D11.2 (A), J29.2, J29.4, J29.12, J29.14, J29.16, J29.18, J29.70, J29.72, J29.74
GND: H3.1, H5.1, J29.1, J29.3, J29.9, J29.15, J29.21, J29.27, J29.33, J29.39, J29.45, J29.51, J29.57, J29.71, J29.73, J29.75, J29.S1 (SHIELD), J29.S2 (SHIELD)
unnamed: D11.1 (K), R82.1
unnamed: J29.10, R82.2
PCIE_CLK_N: J29.53
PCIE_CLK_P: J29.55
PCIE_CLK_nREQ: J29.52
PCIE_RX_N: J29.41
PCIE_RX_P: J29.43
PCIE_TX_N: J29.47
PCIE_TX_P: J29.49
PCIE_nRST: J29.50

Notes on the sheet:
NOTES: ----- - M.2 takes a maximum of +3.3v@3A - Pinout Reference: https://media.digikey.com/pdf/Data_Sheets/Viking_PDFs/PSFNP5xxxx5xxx_C.pdf - Pins 59-66 are missing - Key M
M.2 Connector - 1x PCIe interface
