rickcox/Hepta-Pi/RTC.kicad_sch

## KiCad design RTC.kicad_sch (2023-05-14)

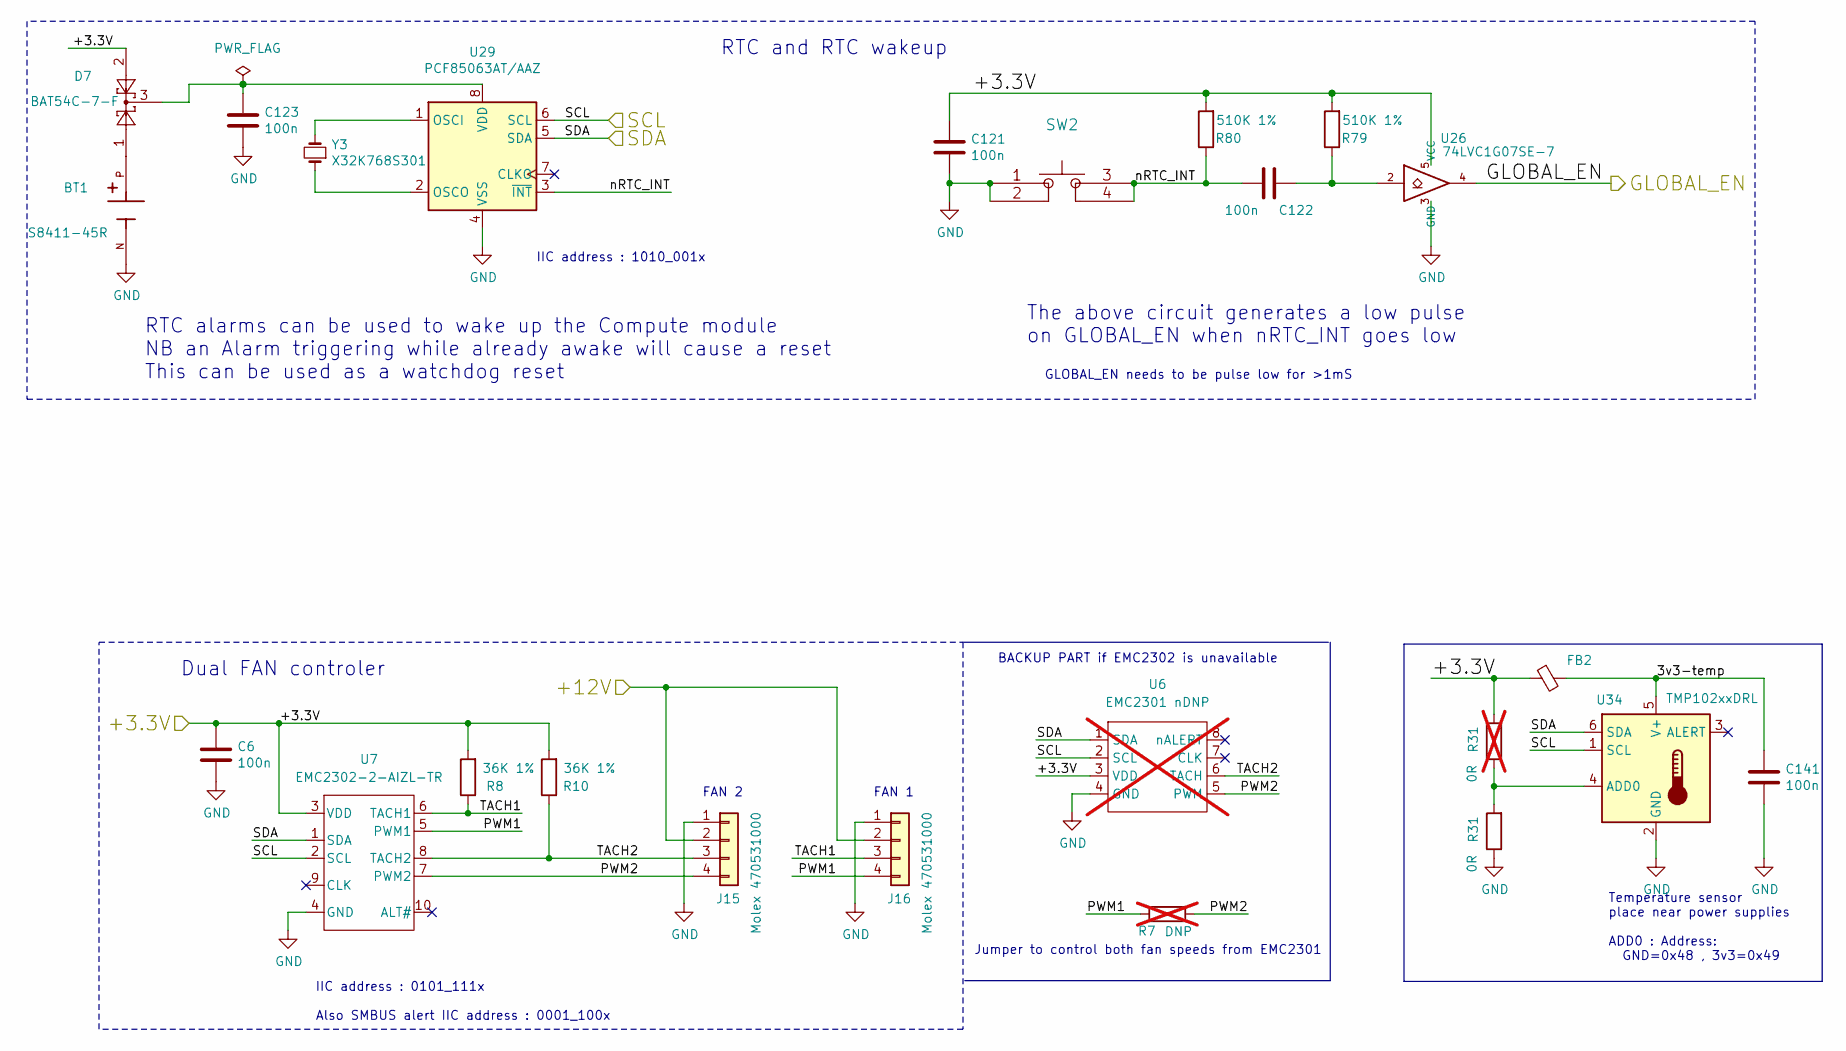
[picture p19: schematic RTC.kicad_sch]

Parts:
BT1: S8411-45R; BAT_S8411-45R; LCSC Part Number C238068
C6, C121, C122, C123: 100n; C_0402_1005Metric; LCSC Part Number C1525
C141: 100n; C_0603_1608Metric; LCSC Part Number C14663
D7: BAT54C-7-F; SOT-23; LCSC Part Number C181200
FB2: FerriteBead_Small; R_0603_1608Metric; LCSC Part Number C108301
J15, J16: Molex 470531000; FanPinHeader_1x04_P2.54mm_Vertical
R7: DNP; R_0603_1608Metric_Pad0.98x0.95mm_HandSolder; LCSC Part Number DNP; not fitted
R8, R10: 36K 1%; R_0603_1608Metric; LCSC Part Number C23147
R31: 0R; R_0603_1608Metric; LCSC Part Number C21189
R79, R80: 510K 1%; R_0603_1608Metric; LCSC Part Number C23192
SW2: pushButton-PTS647SM38SMTR2LFS; Part Description Tact Sw SPST-NO Top Actuated SMT 4.5mmX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; LCSC Part Number C2689502
U6: EMC2301 nDNP; MSOP-8_3x3mm_P0.65mm; Part Description IC MOTOR/FAN DRIVER 3V-3.6V 8MSOP; LCSC Part Number DNP; not fitted
U7: EMC2302-2-AIZL-TR; MSOP-10_3x3mm_P0.5mm; Part Description DUAL IC MOTOR/FAN DRIVER 3V-3.6V 10MSOP; LCSC Part Number C626970
U26: 74LVC1G07SE-7; SOT-353_SC-70-5; LCSC Part Number C67531
U29: PCF85063AT/AAZ; SOIC-8_3.9x4.9mm_P1.27mm; LCSC Part Number C2157792
U34: TMP102xxDRL; SOT-563; Part Description TEMP SENSOR I2C SOT-563
Y3: X32K768S301; Crystal_SMD_3215-2Pin_3.2x1.5mm; LCSC Part Number C32346

Connections:
3v3-temp: C141.1, FB2.2, U34.5 (V+)
+3.3V: C6.1, C121.1, D7.2, FB2.1, R8.2, R10.2, R31.2, R79.2, R80.2, U6.3 (VDD), U7.3 (VDD), U26.5 (VCC)
+12V: J15.2, J16.2
GLOBAL_EN: U26.4
GND: BT1.N, C6.2, C121.2, C123.2, C141.2, J15.1, J16.1, R31.1, SW2.1, SW2.2, U6.4 (GND), U7.4 (GND), U26.3 (GND), U29.4 (VSS), U34.2 (GND)
unnamed: BT1.P, D7.1
unnamed: C122.1, R79.1, U26.2
unnamed: C123.1, D7.3, U29.8 (VDD)
unnamed: R31.1, R31.2, U34.4 (ADD0)
unnamed: U29.1 (OSCI), Y3.2
unnamed: U29.2 (OSCO), Y3.1
PWM1: J16.4, R7.1, U7.5 (PWM1)
PWM2: J15.4, R7.2, U6.5 (PWM), U7.7 (PWM2)
SCL: U6.2 (SCL), U7.2 (SCL), U29.6 (SCL), U34.1 (SCL)
SDA: U6.1 (SDA), U7.1 (SDA), U29.5 (SDA), U34.6 (SDA)
TACH1: J16.3, R8.1, U7.6 (TACH1)
TACH2: J15.3, R10.1, U6.6 (TACH), U7.8 (TACH2)
nRTC_INT: C122.2, R80.1, SW2.3, SW2.4, U29.3 (~INT)

Notes on the sheet:
The above circuit generates a low pulse on GLOBAL_EN when nRTC_INT goes low
RTC alarms can be used to wake up the Compute module NB an Alarm triggering while already awake will cause a reset This can be used as a watchdog reset
GLOBAL_EN needs to be pulse low for >1mS
Also SMBUS alert IIC address : 0001_100x
FAN 1
Temperature sensor place near power supplies ADD0 : Address: GND=0x48 , 3v3=0x49
BACKUP PART if EMC2302 is unavailable
Dual FAN controler
Jumper to control both fan speeds from EMC2301
RTC and RTC wakeup
IIC address : 0101_111x
IIC address : 1010_001x
FAN 2
