rickcox/Hepta-Pi/Radxa_connr.kicad_sch

## KiCad design Radxa_connr.kicad_sch (2023-05-14)

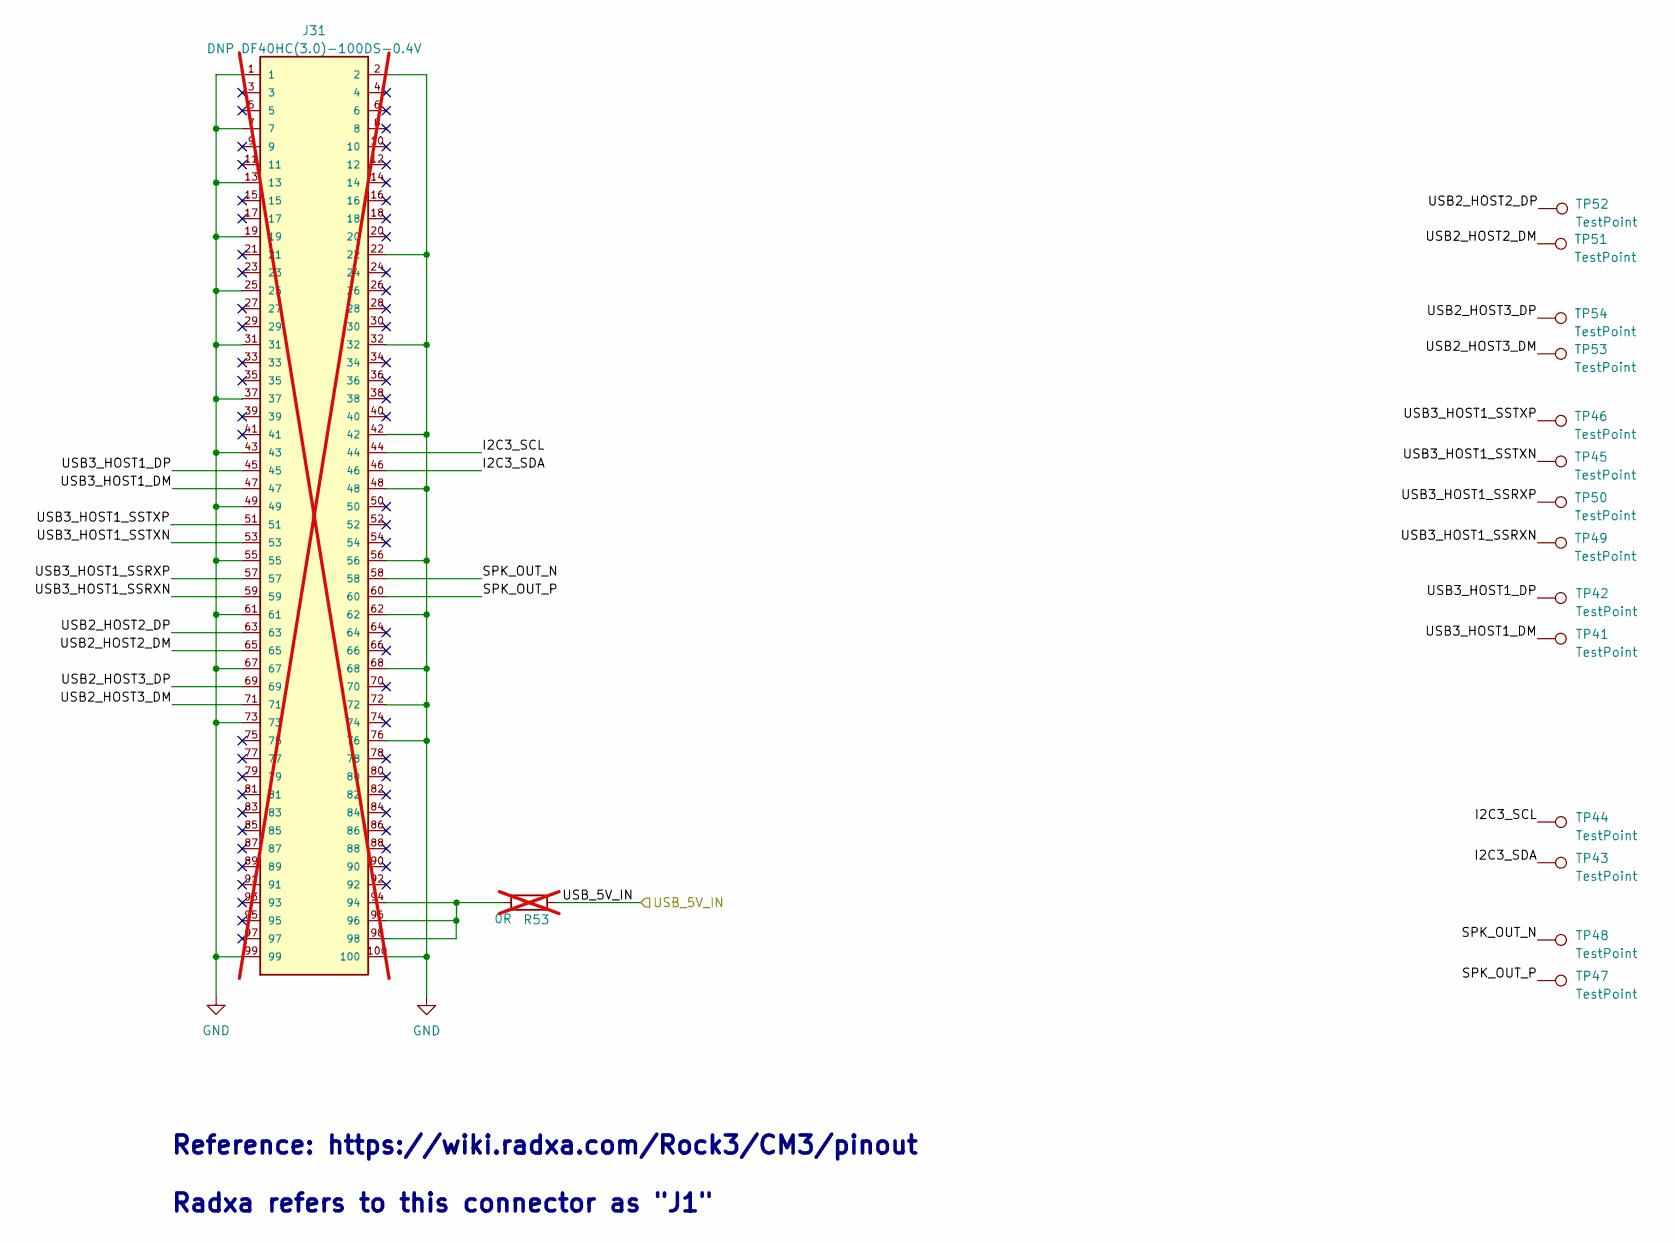
[picture p20: schematic Radxa_connr.kicad_sch]

Parts:
J31: DNP DF40HC(3.0)-100DS-0.4V; HRS_DF40HC(3.0)-100DS-0.4V; LCSC Part Number DNP; not fitted
R53: 0R; R_0603_1608Metric_Pad0.98x0.95mm_HandSolder; LCSC Part Number C21189; not fitted
TP41, TP42, TP43, TP44, TP45, TP46, TP47, TP48, TP49, TP50, TP51, TP52, TP53, TP54: TestPoint; TestPoint_Pad_D1.5mm; LCSC Part Number DNP

Connections:
GND: J31.1, J31.2, J31.7, J31.13, J31.19, J31.22, J31.25, J31.31, J31.32, J31.37, J31.42, J31.43, J31.48, J31.49, J31.55, J31.56, J31.61, J31.62, J31.67, J31.68, J31.72, J31.73, J31.76, J31.99, J31.100
I2C3_SCL: J31.44, TP44.1
I2C3_SDA: J31.46, TP43.1
unnamed: J31.94, J31.96, J31.98, R53.2
SPK_OUT_N: J31.58, TP48.1
SPK_OUT_P: J31.60, TP47.1
USB2_HOST2_DM: J31.65, TP51.1
USB2_HOST2_DP: J31.63, TP52.1
USB2_HOST3_DM: J31.71, TP53.1
USB2_HOST3_DP: J31.69, TP54.1
USB3_HOST1_DM: J31.47, TP41.1
USB3_HOST1_DP: J31.45, TP42.1
USB3_HOST1_SSRXN: J31.59, TP49.1
USB3_HOST1_SSRXP: J31.57, TP50.1
USB3_HOST1_SSTXN: J31.53, TP45.1
USB3_HOST1_SSTXP: J31.51, TP46.1
USB_5V_IN: R53.1

Notes on the sheet:
Reference: https://wiki.radxa.com/Rock3/CM3/pinout Radxa refers to this connector as "J1"
