rickcox/Hepta-Pi/USB2-HUB.kicad_sch

## KiCad design USB2-HUB.kicad_sch (2023-05-14)

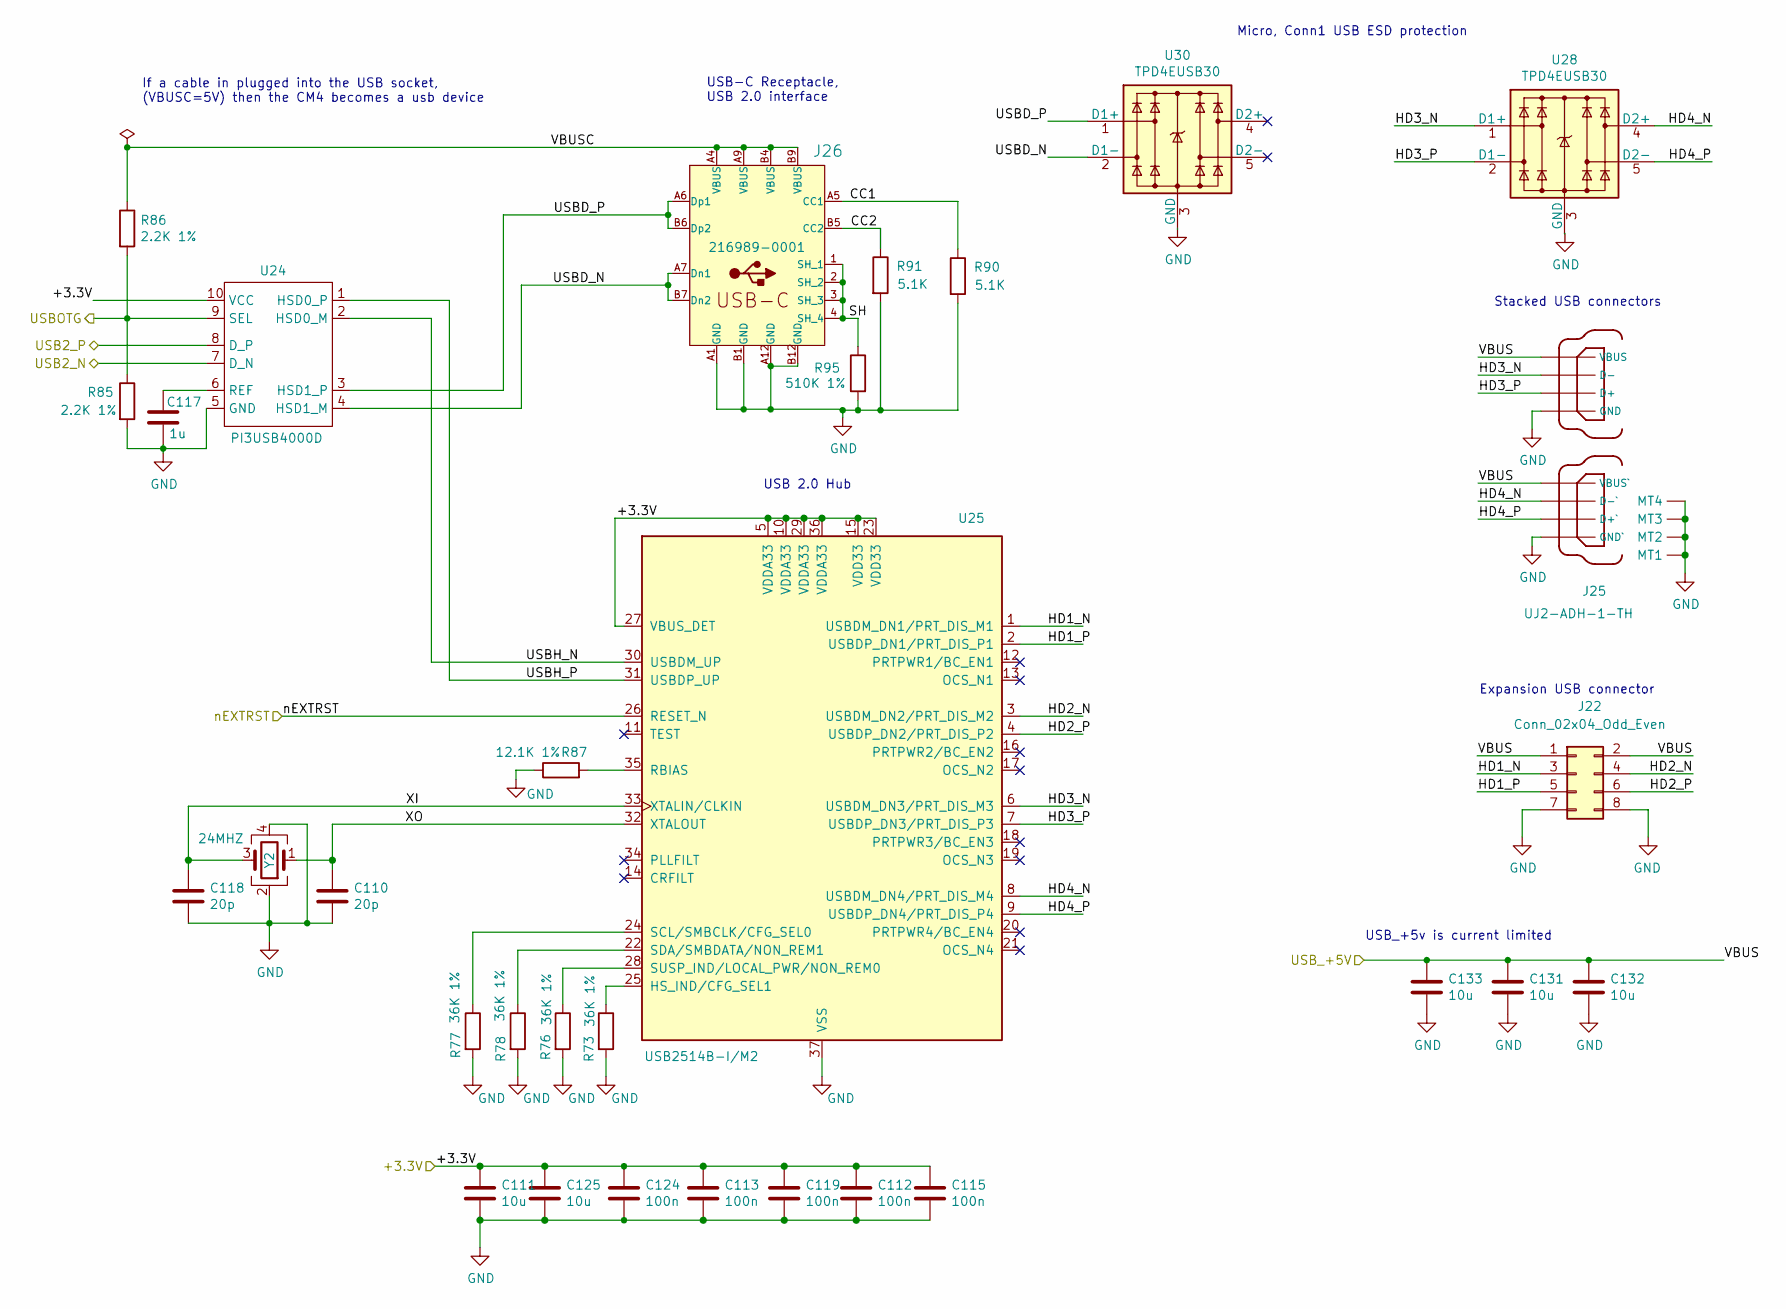
[picture p21: schematic USB2-HUB.kicad_sch]

Parts:
C110, C118: 20p; C_0603_1608Metric; LCSC Part Number C1648
C111, C125, C131, C132, C133: 10u; C_0603_1608Metric; LCSC Part Number C19702
C112, C113, C115, C119, C124: 100n; C_0402_1005Metric; LCSC Part Number C1525
C117: 1u; C_0603_1608Metric; LCSC Part Number C15849
J22: Conn_02x04_Odd_Even; PinHeader_2x04_P2.54mm_Vertical; LCSC Part Number C124386
J25: UJ2-ADH-1-TH; MOLEX_USB_67298-4090; LCSC Part Number C12049
J26: 216989-0001; Molex-216989-0001-MFG; Part Description USB-C female receptacle RA
R73, R76, R77, R78: 36K 1%; R_0603_1608Metric; LCSC Part Number C23147
R85, R86: 2.2K 1%; R_0603_1608Metric; LCSC Part Number C4190
R87: 12.1K 1%; R_0603_1608Metric; LCSC Part Number C22864
R90, R91: 5.1K; R_0603_1608Metric; LCSC Part Number C23186
R95: 510K 1%; R_0603_1608Metric; LCSC Part Number C23192
U24: PI3USB4000D; Texas_R-PUQFN-N10; LCSC Part Number C3656785
U25: USB2514B-I/M2; QFN-36-1EP_6x6mm_P0.5mm_EP3.7x3.7mm; LCSC Part Number C16251
U28, U30: TPD4EUSB30; USON-10_2.5x1.0mm_P0.5mm; LCSC Part Number C558427
Y2: 24MHZ; Crystal_SMD_3225-4Pin_3.2x2.5mm; LCSC Part Number C70571

Connections:
+3.3V: C111.1, C112.1, C113.1, C115.1, C119.1, C124.1, C125.1, U24.10 (VCC), U25.5 (VDDA33), U25.10 (VDDA33), U25.15 (VDD33), U25.23 (VDD33), U25.27 (VBUS_DET), U25.29 (VDDA33), U25.36 (VDDA33)
CC1: J26.A5 (CC1), R90.1
CC2: J26.B5 (CC2), R91.1
GND: C110.2, C111.2, C112.2, C113.2, C115.2, C117.2, C118.2, C119.2, C124.2, C125.2, C131.2, C132.2, C133.2, J22.7, J22.8, J25.4 (GND`), J25.8 (GND), J25.MT1, J25.MT2, J25.MT3, J25.MT4, J26.A1 (GND), J26.A12 (GND), J26.B1 (GND), J26.B12 (GND), R73.2, R76.2, R77.2, R78.2, R85.2, R87.1, R90.2, R91.2, R95.2, U24.5 (GND), U25.37 (VSS), U28.3 (GND), U28.8 (GND), U30.3 (GND), U30.8 (GND), Y2.2, Y2.4
HD1_N: J22.3, U25.1 (USBDM_DN1/PRT_DIS_M1)
HD1_P: J22.5, U25.2 (USBDP_DN1/PRT_DIS_P1)
HD2_N: J22.4, U25.3 (USBDM_DN2/PRT_DIS_M2)
HD2_P: J22.6, U25.4 (USBDP_DN2/PRT_DIS_P2)
HD3_N: J25.6 (D-), U25.6 (USBDM_DN3/PRT_DIS_M3), U28.1 (D1+), U28.10
HD3_P: J25.7 (D+), U25.7 (USBDP_DN3/PRT_DIS_P3), U28.2 (D1-), U28.9
HD4_N: J25.2 (D-`), U25.8 (USBDM_DN4/PRT_DIS_M4), U28.4 (D2+), U28.7
HD4_P: J25.3 (D+`), U25.9 (USBDP_DN4/PRT_DIS_P4), U28.5 (D2-), U28.6
unnamed: C117.1, U24.6 (REF)
unnamed: R73.1, U25.25 (HS_IND/CFG_SEL1)
unnamed: R76.1, U25.28 (SUSP_IND/LOCAL_PWR/NON_REM0)
unnamed: R77.1, U25.24 (SCL/SMBCLK/CFG_SEL0)
unnamed: R78.1, U25.22 (SDA/SMBDATA/NON_REM1)
unnamed: R87.2, U25.35 (RBIAS)
unnamed: U30.4 (D2+), U30.7
unnamed: U30.5 (D2-), U30.6
SH: J26.1 (SH_1), J26.2 (SH_2), J26.3 (SH_3), J26.4 (SH_4), R95.1
USB2_N: U24.7 (D_N)
USB2_P: U24.8 (D_P)
USBD_N: J26.A7 (Dn1), J26.B7 (Dn2), U24.4 (HSD1_M), U30.2 (D1-), U30.9
USBD_P: J26.A6 (Dp1), J26.B6 (Dp2), U24.3 (HSD1_P), U30.1 (D1+), U30.10
USBH_N: U24.2 (HSD0_M), U25.30 (USBDM_UP)
USBH_P: U24.1 (HSD0_P), U25.31 (USBDP_UP)
USBOTG: R85.1, R86.2, U24.9 (SEL)
USB_+5V: C131.1, C132.1, C133.1, J22.1, J22.2, J25.1 (VBUS`), J25.5 (VBUS)
VBUSC: J26.A4 (VBUS), J26.A9 (VBUS), J26.B4 (VBUS), J26.B9 (VBUS), R86.1
XI: C118.1, U25.33 (XTALIN/CLKIN), Y2.3
XO: C110.1, U25.32 (XTALOUT), Y2.1
nEXTRST: U25.26 (RESET_N)

Notes on the sheet:
Micro, Conn1 USB ESD protection
Stacked USB connectors
Expansion USB connector
USB 2.0 Hub
USB-C Receptacle, USB 2.0 interface
USB_+5v is current limited
If a cable in plugged into the USB socket, (VBUSC=5V) then the CM4 becomes a usb device
