rickcox/Hepta-Pi/cm-sum.kicad_sch

## KiCad design cm-sum.kicad_sch (2023-05-14)

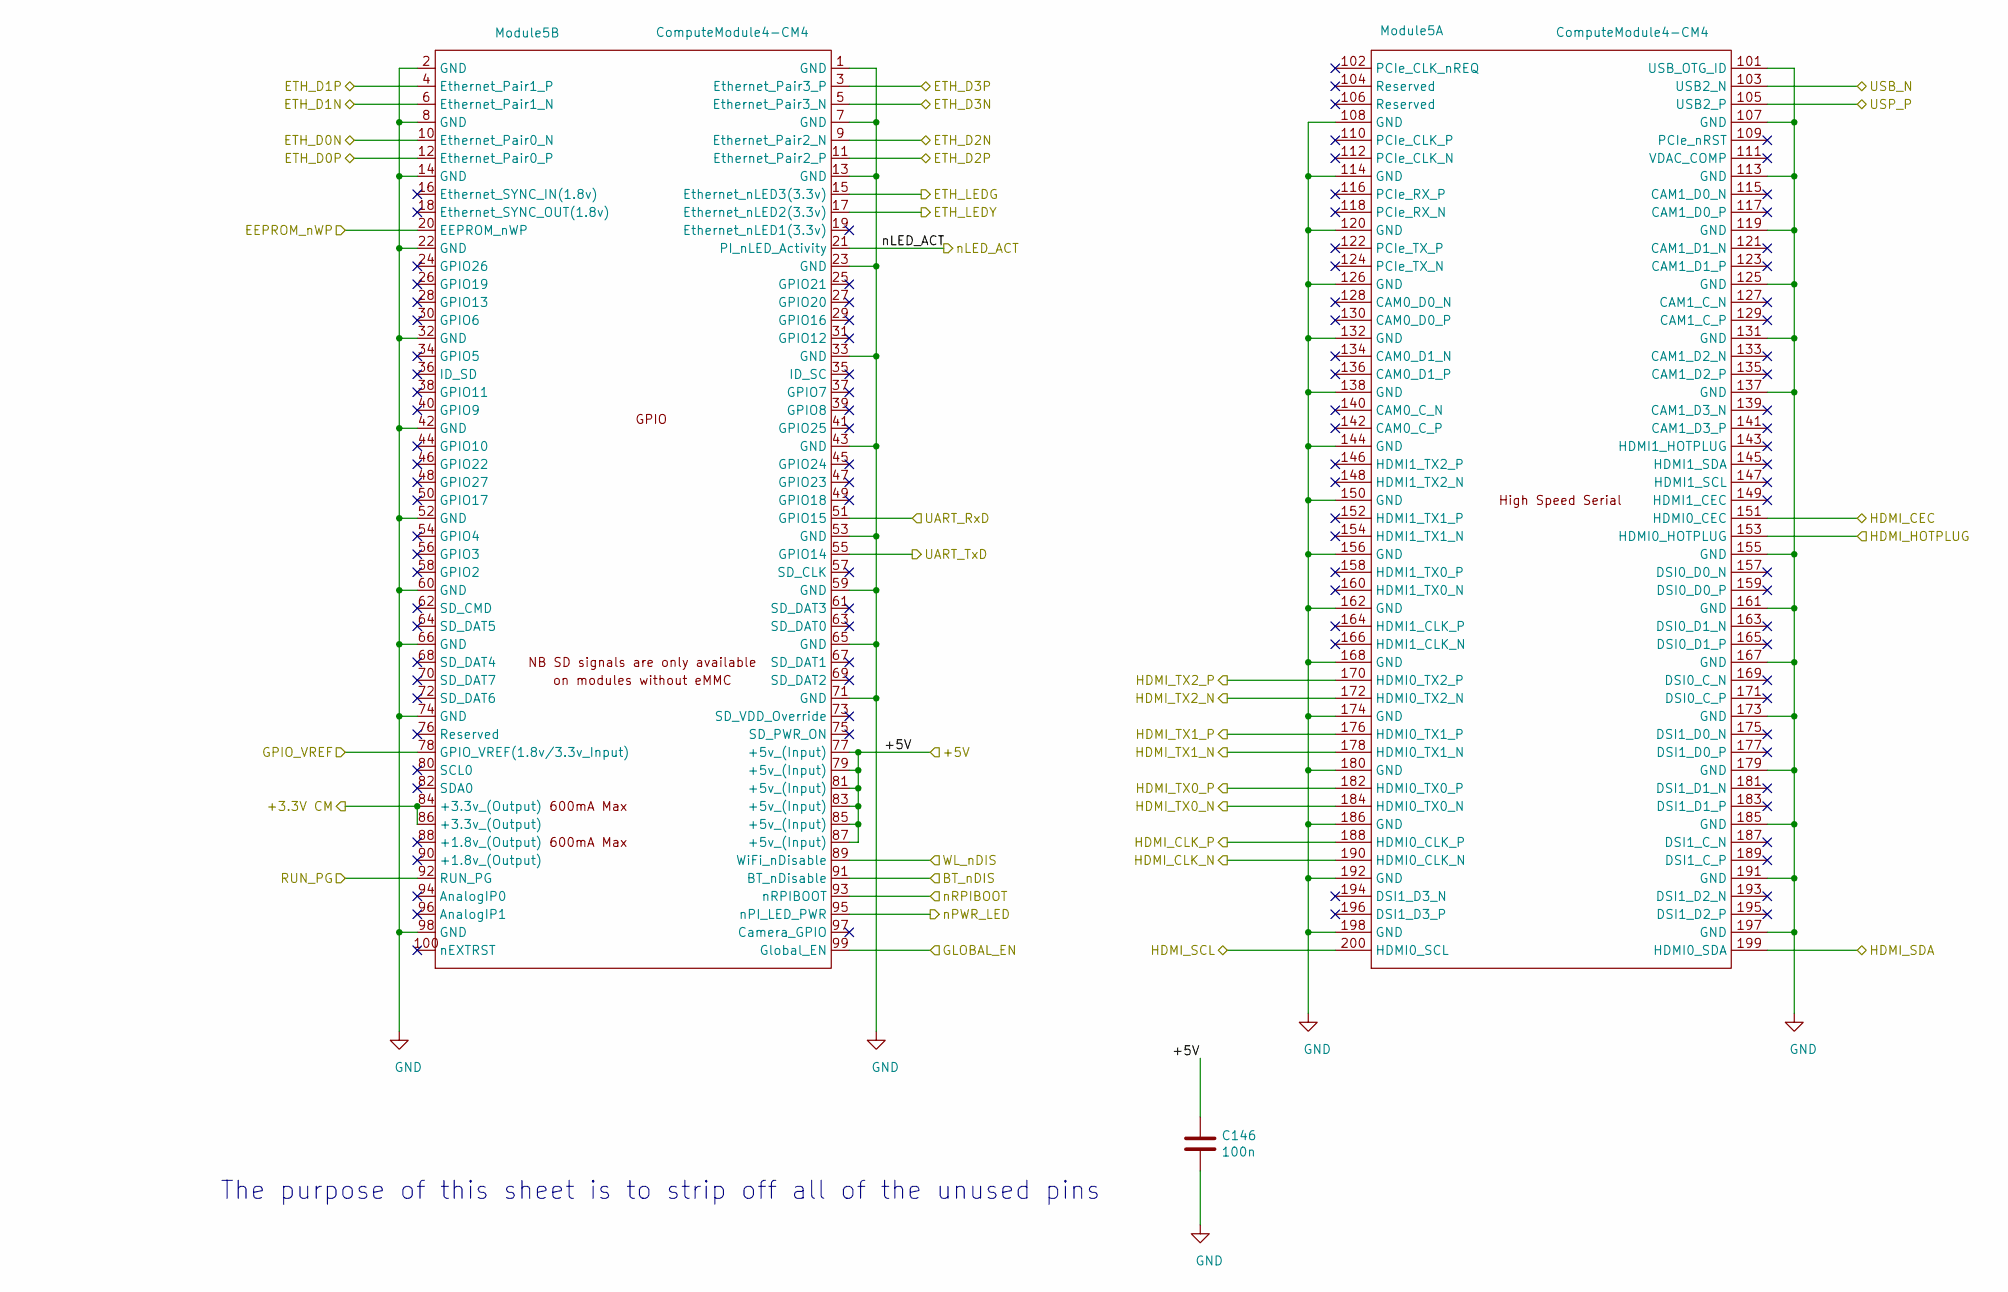
[picture p22: schematic cm-sum.kicad_sch]

Parts:
C146: 100n; C_0402_1005Metric; LCSC Part Number C1525
Module5: ComputeModule4-CM4; Raspberry-Pi-4-Compute-Module

Connections:
+3.3V CM: Module5.84 (+3.3v_(Output)), Module5.86 (+3.3v_(Output))
+5V: C146.1, Module5.77 (+5v_(Input)), Module5.79 (+5v_(Input)), Module5.81 (+5v_(Input)), Module5.83 (+5v_(Input)), Module5.85 (+5v_(Input)), Module5.87 (+5v_(Input))
BT_nDIS: Module5.91 (BT_nDisable)
EEPROM_nWP: Module5.20 (EEPROM_nWP)
ETH_D0N: Module5.10 (Ethernet_Pair0_N)
ETH_D0P: Module5.12 (Ethernet_Pair0_P)
ETH_D1N: Module5.6 (Ethernet_Pair1_N)
ETH_D1P: Module5.4 (Ethernet_Pair1_P)
ETH_D2N: Module5.9 (Ethernet_Pair2_N)
ETH_D2P: Module5.11 (Ethernet_Pair2_P)
ETH_D3N: Module5.5 (Ethernet_Pair3_N)
ETH_D3P: Module5.3 (Ethernet_Pair3_P)
ETH_LEDG: Module5.15 (Ethernet_nLED3(3.3v))
ETH_LEDY: Module5.17 (Ethernet_nLED2(3.3v))
GLOBAL_EN: Module5.99 (Global_EN)
GND: C146.2, Module5.1 (GND), Module5.2 (GND), Module5.7 (GND), Module5.8 (GND), Module5.13 (GND), Module5.14 (GND), Module5.22 (GND), Module5.23 (GND), Module5.32 (GND), Module5.33 (GND), Module5.42 (GND), Module5.43 (GND), Module5.52 (GND), Module5.53 (GND), Module5.59 (GND), Module5.60 (GND), Module5.65 (GND), Module5.66 (GND), Module5.71 (GND), Module5.74 (GND), Module5.98 (GND), Module5.101 (USB_OTG_ID), Module5.107 (GND), Module5.108 (GND), Module5.113 (GND), Module5.114 (GND), Module5.119 (GND), Module5.120 (GND), Module5.125 (GND), Module5.126 (GND), Module5.131 (GND), Module5.132 (GND), Module5.137 (GND), Module5.138 (GND), Module5.144 (GND), Module5.150 (GND), Module5.155 (GND), Module5.156 (GND), Module5.161 (GND), Module5.162 (GND), Module5.167 (GND), Module5.168 (GND), Module5.173 (GND), Module5.174 (GND), Module5.179 (GND), Module5.180 (GND), Module5.185 (GND), Module5.186 (GND), Module5.191 (GND), Module5.192 (GND), Module5.197 (GND), Module5.198 (GND)
GPIO_VREF: Module5.78 (GPIO_VREF(1.8v/3.3v_Input))
HDMI_CEC: Module5.151 (HDMI0_CEC)
HDMI_CLK_N: Module5.190 (HDMI0_CLK_N)
HDMI_CLK_P: Module5.188 (HDMI0_CLK_P)
HDMI_HOTPLUG: Module5.153 (HDMI0_HOTPLUG)
HDMI_SCL: Module5.200 (HDMI0_SCL)
HDMI_SDA: Module5.199 (HDMI0_SDA)
HDMI_TX0_N: Module5.184 (HDMI0_TX0_N)
HDMI_TX0_P: Module5.182 (HDMI0_TX0_P)
HDMI_TX1_N: Module5.178 (HDMI0_TX1_N)
HDMI_TX1_P: Module5.176 (HDMI0_TX1_P)
HDMI_TX2_N: Module5.172 (HDMI0_TX2_N)
HDMI_TX2_P: Module5.170 (HDMI0_TX2_P)
RUN_PG: Module5.92 (RUN_PG)
UART_RxD: Module5.51 (GPIO15)
UART_TxD: Module5.55 (GPIO14)
USB_N: Module5.103 (USB2_N)
USP_P: Module5.105 (USB2_P)
WL_nDIS: Module5.89 (WiFi_nDisable)
nLED_ACT: Module5.21 (PI_nLED_Activity)
nPWR_LED: Module5.95 (nPI_LED_PWR)
nRPIBOOT: Module5.93 (nRPIBOOT)

Notes on the sheet:
The purpose of this sheet is to strip off all of the unused pins
