rickcox/Hepta-Pi/cm-top.kicad_sch

## KiCad design cm-top.kicad_sch (2023-05-14)

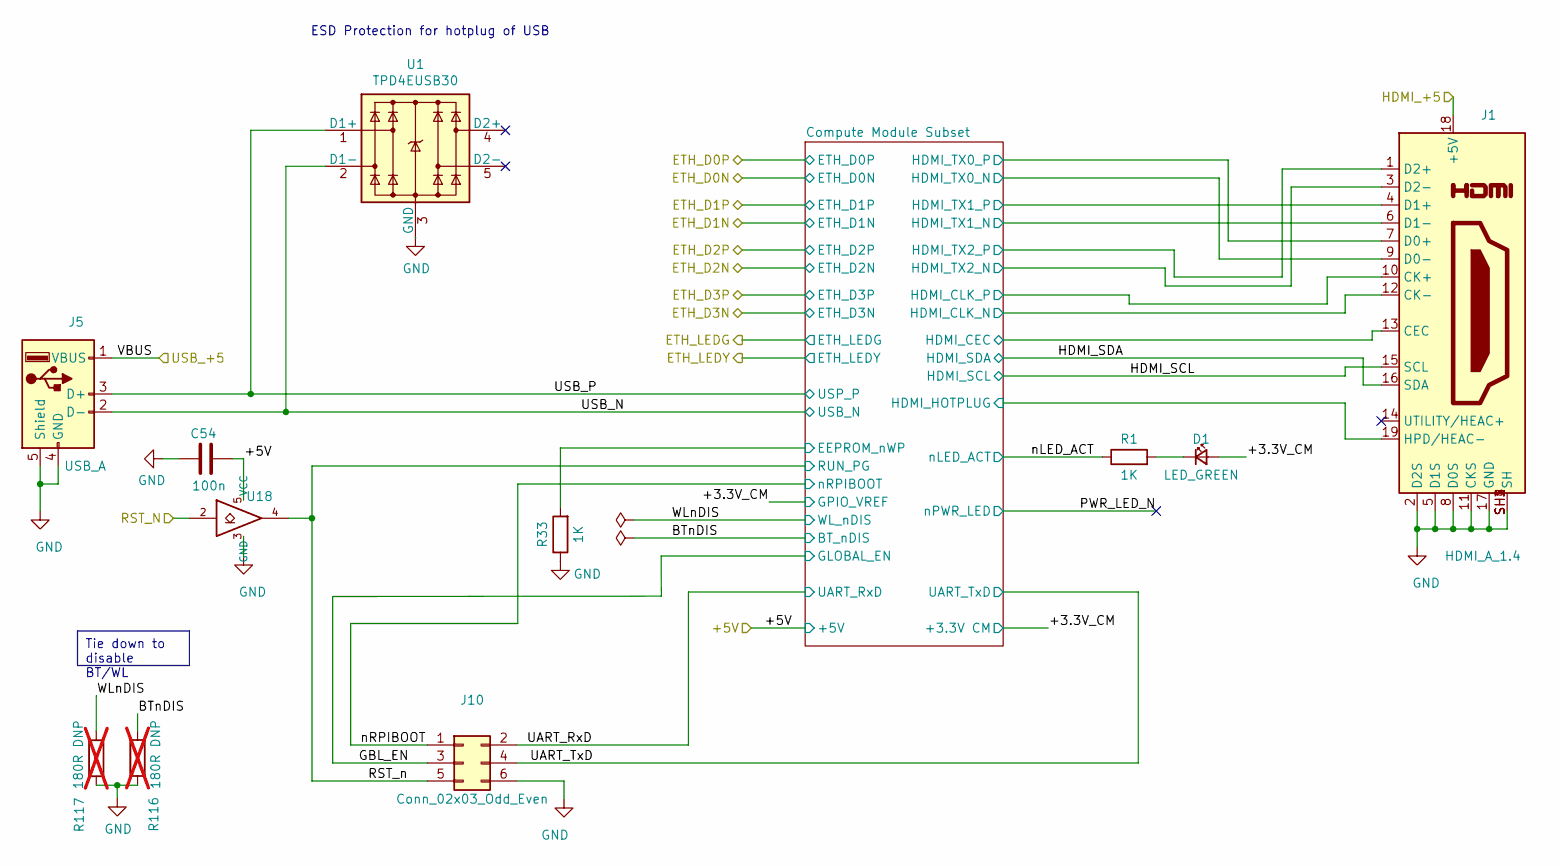
[picture p23: schematic cm-top.kicad_sch]

Parts:
C54: 100n; C_0402_1005Metric; LCSC Part Number C1525
D1: LED_GREEN; LED_0805_2012Metric_Pad1.15x1.40mm_HandSolder; LCSC Part Number C2297
J1: HDMI_A_1.4; EDAC 690-019-298-412; LCSC Part Number C720616
J5: USB_A; USB_A_Wuerth_614004134726_Horizontal; LCSC Part Number C305979
J10: Conn_02x03_Odd_Even; PinHeader_2x03_P2.54mm_Vertical
R1, R33: 1K; R_0603_1608Metric; LCSC Part Number C21190
R116, R117: 180R DNP; R_0603_1608Metric_Pad0.98x0.95mm_HandSolder; LCSC Part Number DNP; not fitted
U1: TPD4EUSB30; USON-10_2.5x1.0mm_P0.5mm; LCSC Part Number C558427
U18: 74LVC1G07SE-7; SOT-353_SC-70-5; LCSC Part Number C67531

Connections:
+3.3V_CM: D1.2 (A)
+5V: C54.1, U18.5 (VCC)
BTnDIS: R116.2
EEPROM_nWP: R33.2
GBL_EN: J10.3
GND: C54.2, J1.2 (D2S), J1.5 (D1S), J1.8 (D0S), J1.11 (CKS), J1.17 (GND), J1.SH1 (SH), J1.SH2 (SH), J1.SH3 (SH), J1.SH4 (SH), J5.4 (GND), J5.5 (Shield), J10.6, R33.1, R116.1, R117.1, U1.3 (GND), U1.8 (GND), U18.3 (GND)
HDMI_+5: J1.18 (+5V)
HDMI_CEC: J1.13 (CEC)
HDMI_CLK_N: J1.12 (CK-)
HDMI_CLK_P: J1.10 (CK+)
HDMI_HOTPLUG: J1.19 (HPD/HEAC-)
HDMI_SCL: J1.15 (SCL)
HDMI_SDA: J1.16 (SDA)
HDMI_TX0_N: J1.9 (D0-)
HDMI_TX0_P: J1.7 (D0+)
HDMI_TX1_N: J1.6 (D1-)
HDMI_TX1_P: J1.4 (D1+)
HDMI_TX2_N: J1.3 (D2-)
HDMI_TX2_P: J1.1 (D2+)
unnamed: D1.1 (K), R1.2
unnamed: U1.4 (D2+), U1.7
unnamed: U1.5 (D2-), U1.6
RST_N: J10.5, U18.2, U18.4
UART_RxD: J10.2
UART_TxD: J10.4
USB_+5: J5.1 (VBUS)
USB_N: J5.2 (D-), U1.2 (D1-), U1.9
USB_P: J5.3 (D+), U1.1 (D1+), U1.10
WLnDIS: R117.2
nLED_ACT: R1.1
nRPIBOOT: J10.1

Notes on the sheet:
Tie down to disable BT/WL
ESD Protection for hotplug of USB
