rickcox/Hepta-Pi/enet-8c.kicad_sch

## KiCad design enet-8c.kicad_sch (2023-05-14)

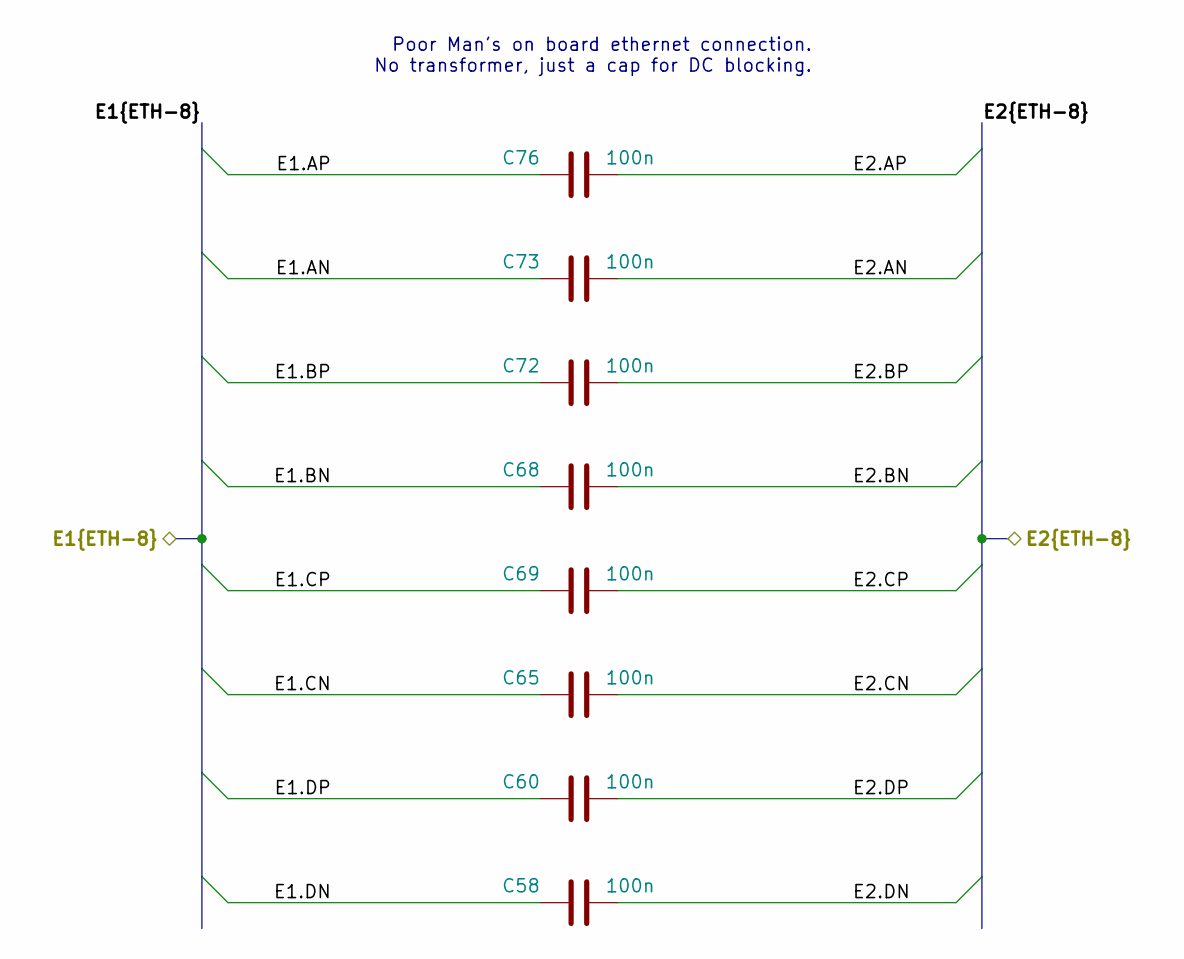
[picture p24: schematic enet-8c.kicad_sch]

Parts:
C58, C60, C65, C68, C69, C72, C73, C76: 100n; C_0603_1608Metric; LCSC Part Number C14663

Connections:
E1.AN: C73.1
E1.AP: C76.1
E1.BN: C68.1
E1.BP: C72.1
E1.CN: C65.1
E1.CP: C69.1
E1.DN: C58.1
E1.DP: C60.1
E2.AN: C73.2
E2.AP: C76.2
E2.BN: C68.2
E2.BP: C72.2
E2.CN: C65.2
E2.CP: C69.2
E2.DN: C58.2
E2.DP: C60.2

Notes on the sheet:
Poor Man's on board ethernet connection. No transformer, just a cap for DC blocking.
