rickcox/Hepta-Pi/enet_on_board.kicad_sch

## KiCad design enet_on_board.kicad_sch (2023-05-14)

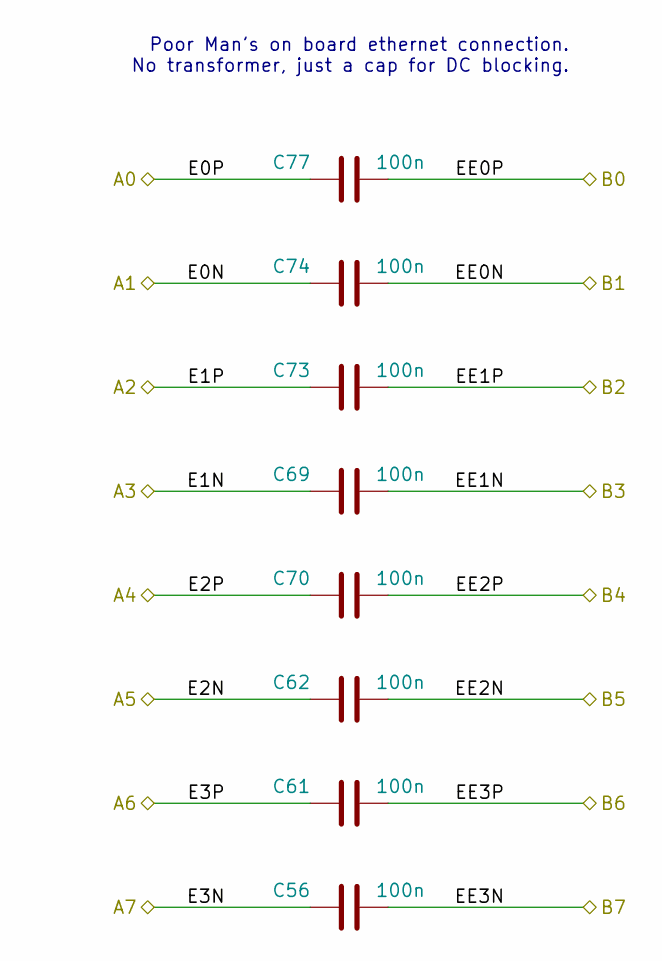
[picture p25: schematic enet_on_board.kicad_sch]

Parts:
C56, C61, C62, C69, C70, C73, C74, C77: 100n; C_0603_1608Metric; LCSC Part Number C14663

Connections:
A0: C77.1
A1: C74.1
A2: C73.1
A3: C69.1
A4: C70.1
A5: C62.1
A6: C61.1
A7: C56.1
B0: C77.2
B1: C74.2
B2: C73.2
B3: C69.2
B4: C70.2
B5: C62.2
B6: C61.2
B7: C56.2

Notes on the sheet:
Poor Man's on board ethernet connection. No transformer, just a cap for DC blocking.
