rickcox/Hepta-Pi/enet_on_board_0R.kicad_sch

## KiCad design enet_on_board_0R.kicad_sch (2023-05-14)

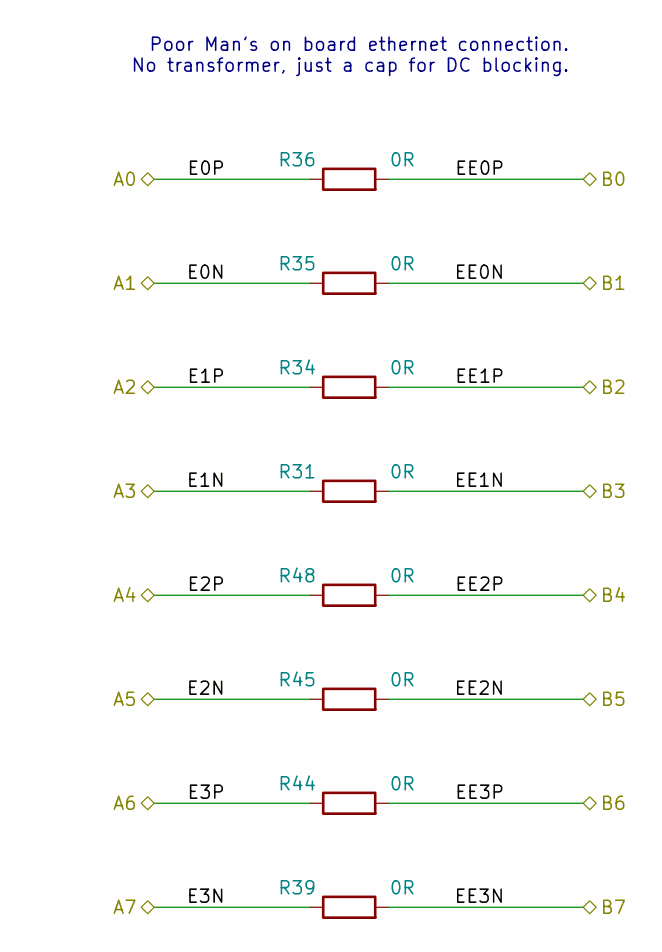
[picture p26: schematic enet_on_board_0R.kicad_sch]

Parts:
R31, R34, R35, R36, R39, R44, R45, R48: 0R; R_0603_1608Metric; LCSC Part Number C21189

Connections:
A0: R36.1
A1: R35.1
A2: R34.1
A3: R31.1
A4: R48.1
A5: R45.1
A6: R44.1
A7: R39.1
B0: R36.2
B1: R35.2
B2: R34.2
B3: R31.2
B4: R48.2
B5: R45.2
B6: R44.2
B7: R39.2

Notes on the sheet:
Poor Man's on board ethernet connection. No transformer, just a cap for DC blocking.
