rickcox/Hepta-Pi/enet_on_board_compact.kicad_sch

## KiCad design enet_on_board_compact.kicad_sch (2023-05-14)

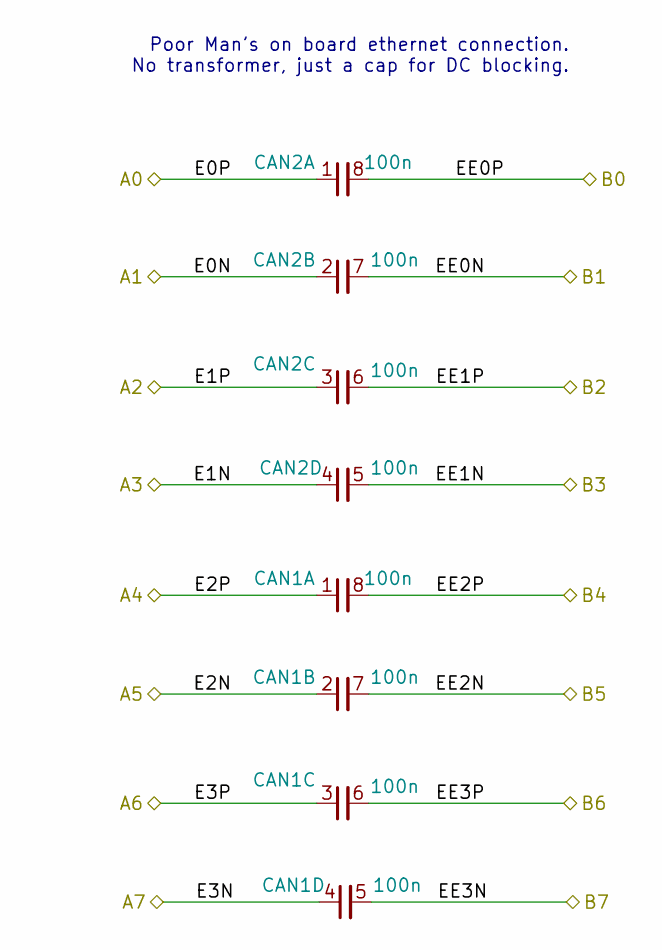
[picture p27: schematic enet_on_board_compact.kicad_sch]

Parts:
CAN1, CAN2: 100n; R_Array_Concave_4x0603; Manuf Partno CA064C104M4RAC7800

Connections:
A0: CAN2.1
A1: CAN2.2
A2: CAN2.3
A3: CAN2.4
A4: CAN1.1
A5: CAN1.2
A6: CAN1.3
A7: CAN1.4
B0: CAN2.8
B1: CAN2.7
B2: CAN2.6
B3: CAN2.5
B4: CAN1.8
B5: CAN1.7
B6: CAN1.6
B7: CAN1.5

Notes on the sheet:
Poor Man's on board ethernet connection. No transformer, just a cap for DC blocking.
