rickcox/Hepta-Pi/enet_sw.kicad_sch

## KiCad design enet_sw.kicad_sch (2023-05-14)

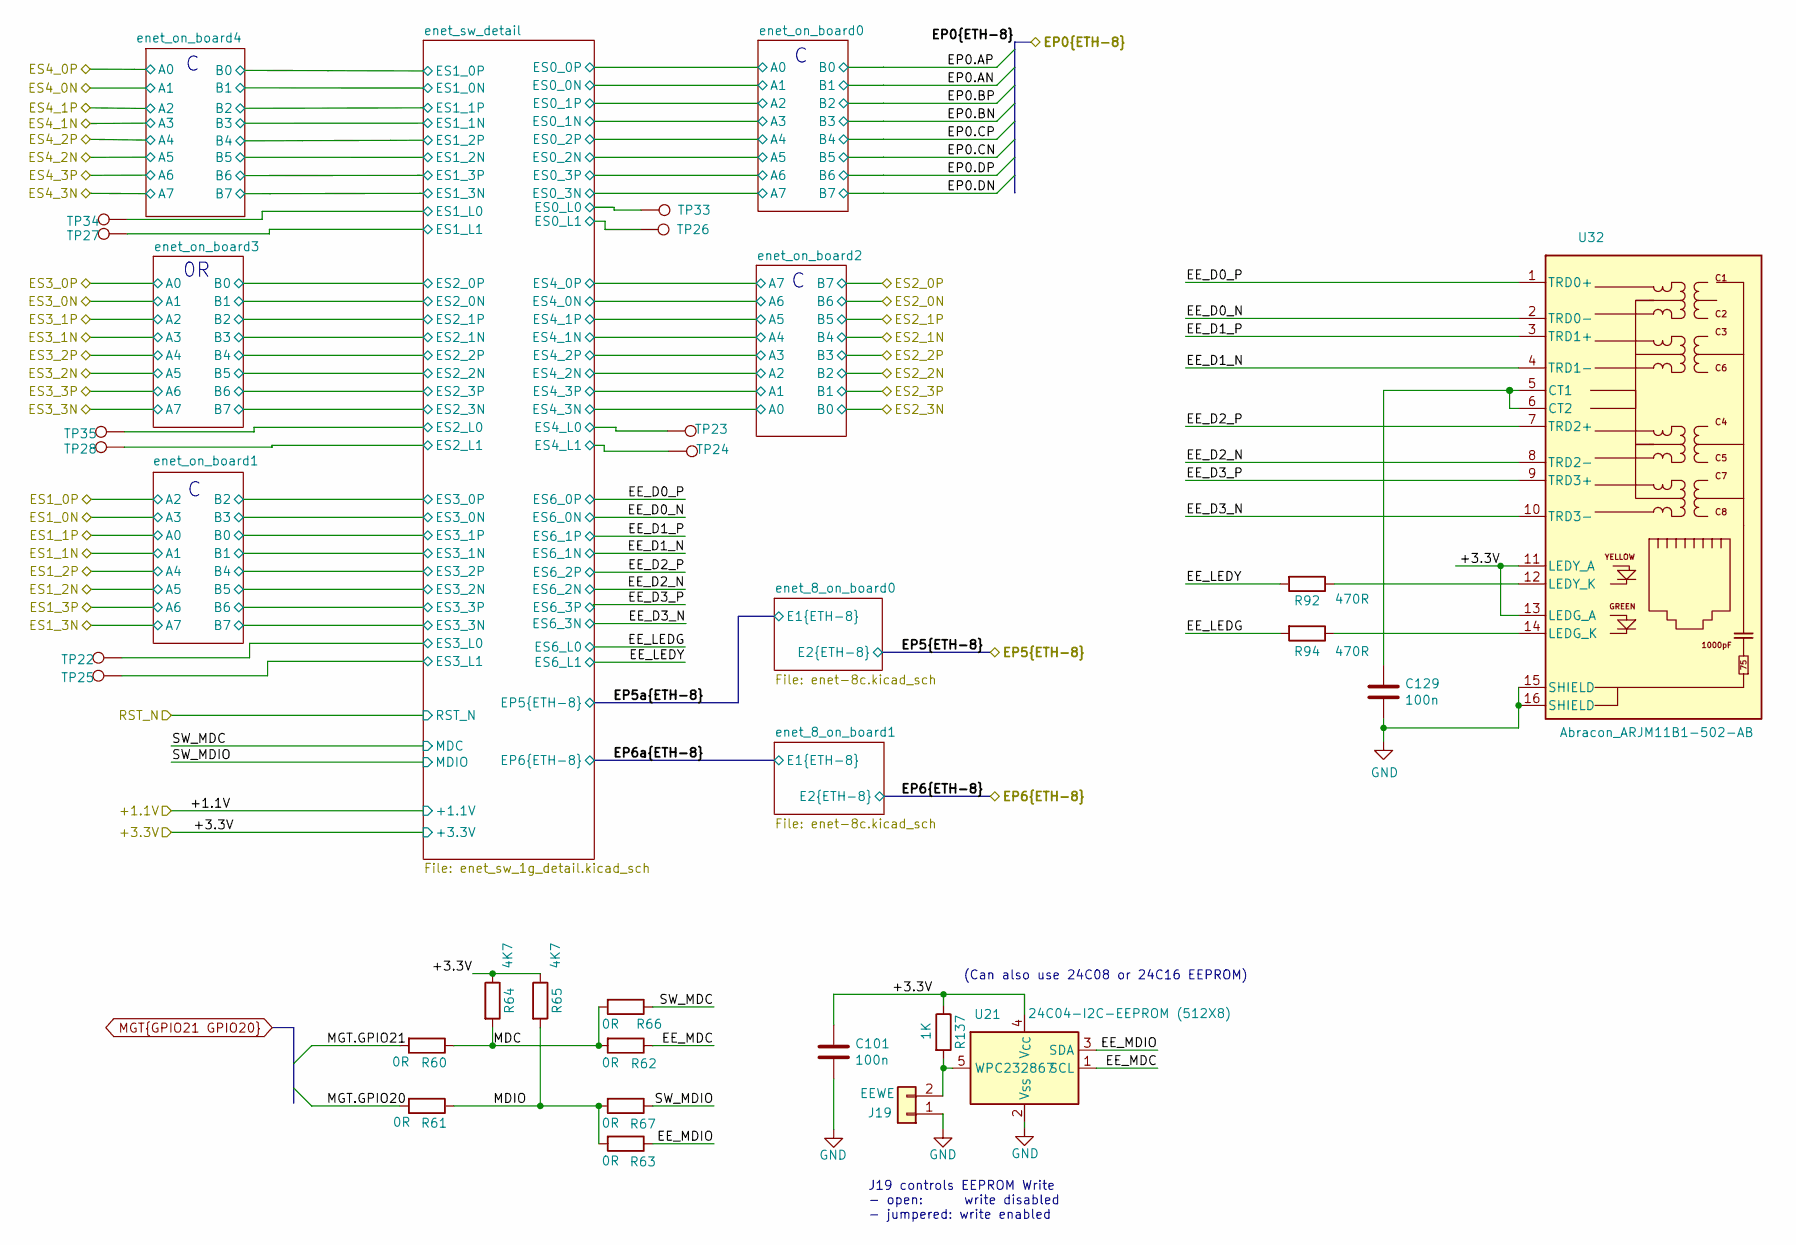
[picture p28: schematic enet_sw.kicad_sch]

Parts:
C101: 100n; C_0402_1005Metric; LCSC Part Number C1525
C129: 100n; C_0603_1608Metric; LCSC Part Number C14663
J19: EEWE; PinHeader_1x02_P2.54mm_Vertical
R60, R61, R62, R63, R66, R67: 0R; R_0603_1608Metric; LCSC Part Number C21189
R64, R65: 4K7; R_0603_1608Metric; LCSC Part Number C99782
R92, R94: 470R; R_0603_1608Metric; LCSC Part Number C23179
R137: 1K; R_0603_1608Metric; LCSC Part Number C21190
TP22, TP23, TP24, TP25, TP26, TP27, TP28, TP33, TP34, TP35: TestPoint; TestPoint_Pad_D1.0mm; LCSC Part Number DNP
U21: 24C04-I2C-EEPROM (512X8); SOT-23-5; Part Description SOT23-5 EEPROM 512X8; LCSC Part Number C232867
U32: Abracon_ARJM11B1-502-AB; ARJM11B1-502-AB; LCSC Part Number C240190

Connections:
+3.3V: C101.1, R64.1, R65.1, R137.1, U21.4 (V_{CC}), U32.11 (LEDY_A), U32.13 (LEDG_A)
EE_D0_N: U32.2 (TRD0-)
EE_D0_P: U32.1 (TRD0+)
EE_D1_N: U32.4 (TRD1-)
EE_D1_P: U32.3 (TRD1+)
EE_D2_N: U32.8 (TRD2-)
EE_D2_P: U32.7 (TRD2+)
EE_D3_N: U32.10 (TRD3-)
EE_D3_P: U32.9 (TRD3+)
EE_LEDG: R94.2
EE_LEDY: R92.2
EE_MDC: R62.1, U21.1 (SCL)
EE_MDIO: R63.1, U21.3 (SDA)
ES0_L0: TP33.1
ES0_L1: TP26.1
ES1_L0: TP34.1
ES1_L1: TP27.1
ES2_L0: TP35.1
ES2_L1: TP28.1
ES3_L0: TP22.1
ES3_L1: TP25.1
ES4_L0: TP23.1
ES4_L1: TP24.1
GND: C101.2, C129.2, J19.1, U21.2 (V_{SS}), U32.15 (SHIELD), U32.16 (SHIELD)
MDC: R60.1, R62.2, R64.2, R66.2
MDIO: R61.1, R63.2, R65.2, R67.2
MGT.GPIO20: R61.2
MGT.GPIO21: R60.2
unnamed: C129.1, U32.5 (CT1), U32.6 (CT2)
unnamed: J19.2, R137.2, U21.5 (WP)
unnamed: R92.1, U32.12 (LEDY_K)
unnamed: R94.1, U32.14 (LEDG_K)
SW_MDC: R66.1
SW_MDIO: R67.1

Notes on the sheet:
J19 controls EEPROM Write - open: write disabled - jumpered: write enabled
(Can also use 24C08 or 24C16 EEPROM)
