rickcox/Hepta-Pi/enet_sw_1g_detail.kicad_sch

## KiCad design enet_sw_1g_detail.kicad_sch (2023-05-14)

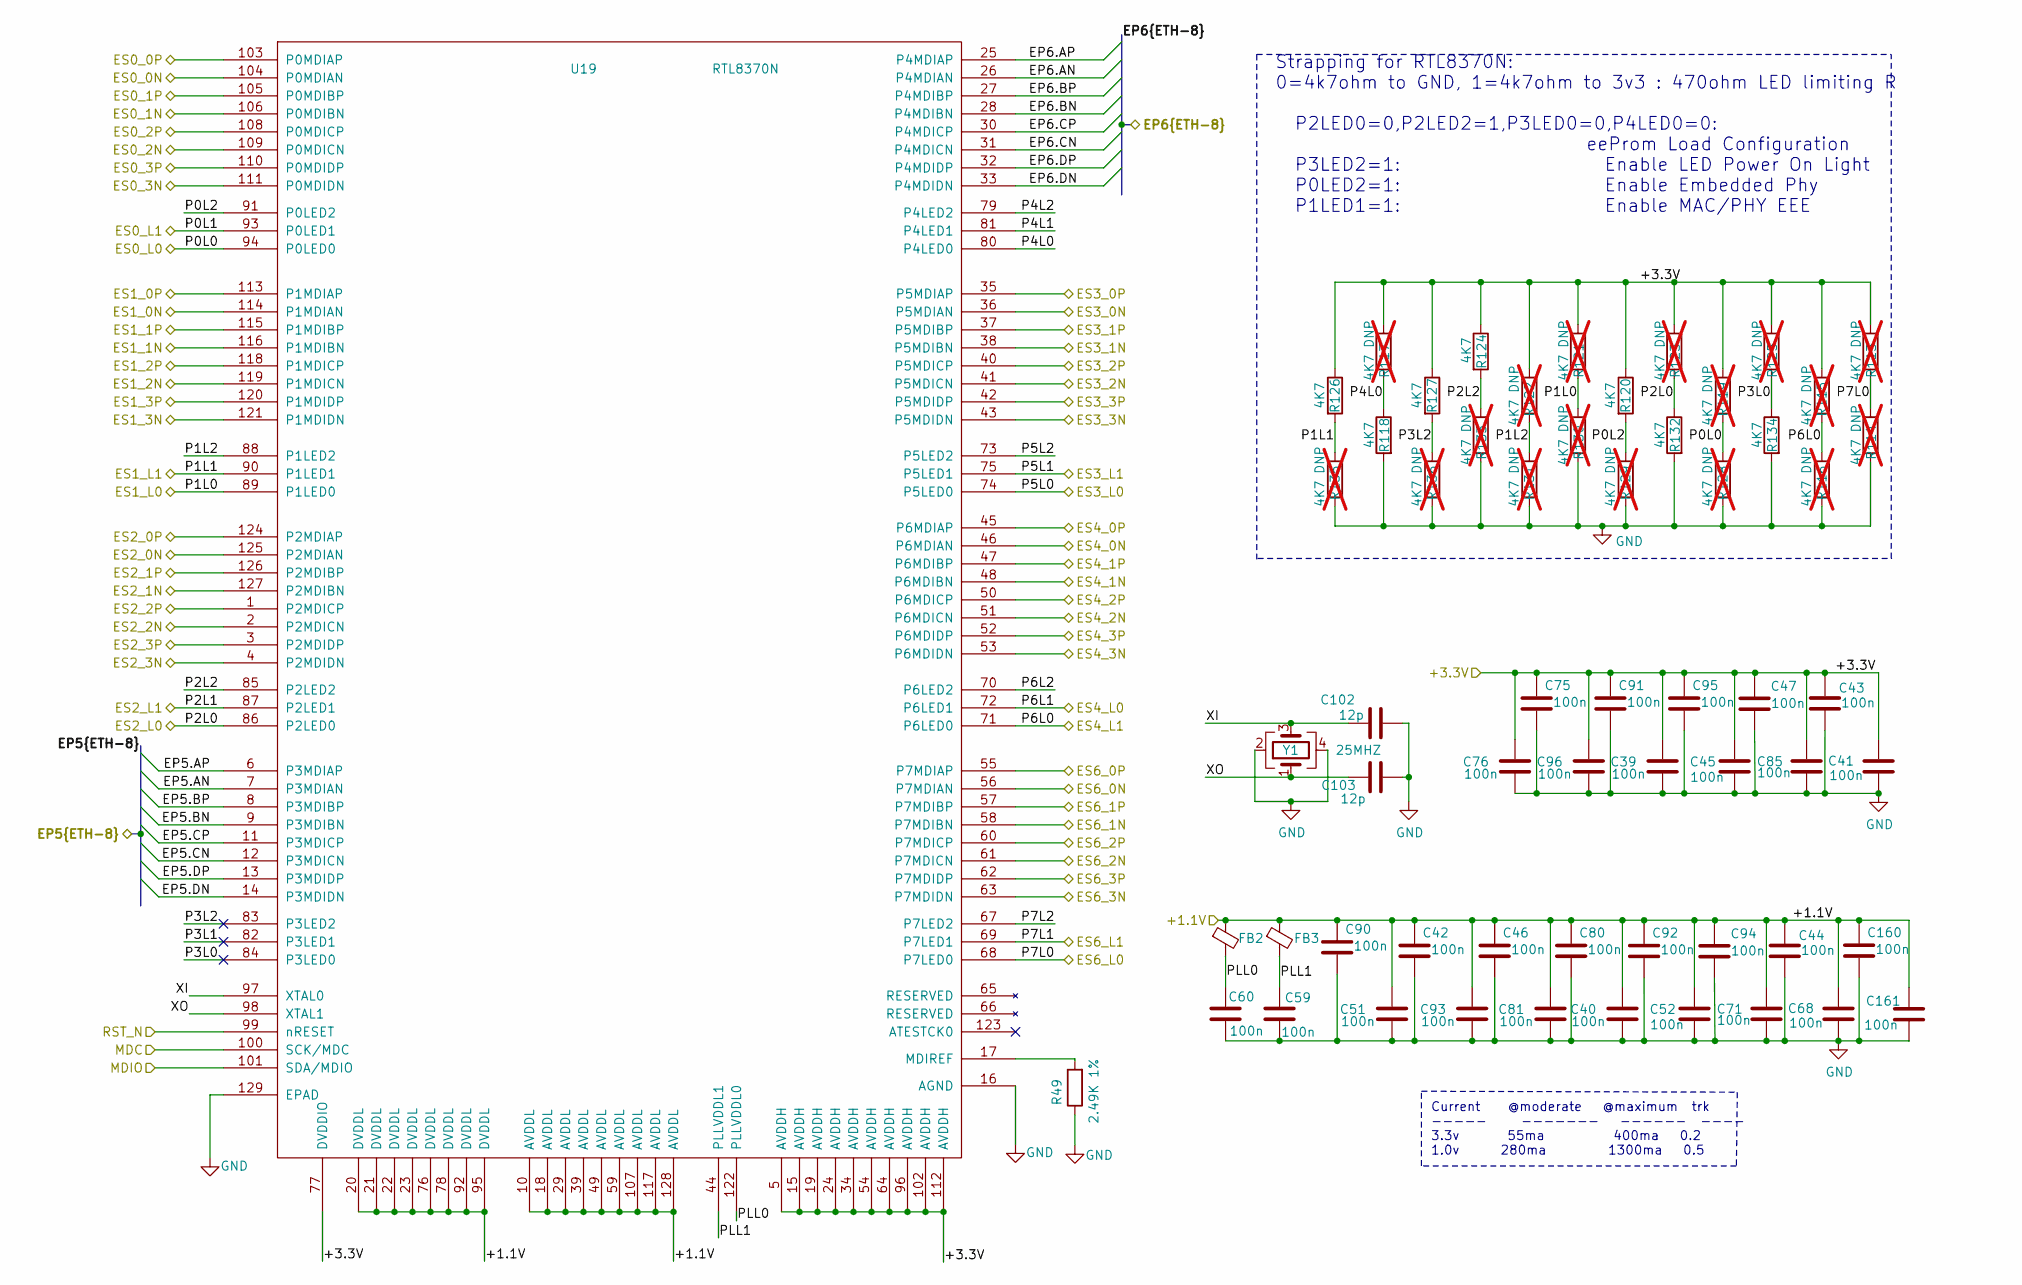
[picture p29: schematic enet_sw_1g_detail.kicad_sch]

Parts:
C39, C40, C41, C42, C43, C44, C45, C46, C47, C51, C52, C59, C60, C68, C71, C75, C76, C80, C81, C85, C90, C91, C92, C93, C94, C95, C96: 100n; C_0402_1005Metric; LCSC Part Number C1525
C102, C103: 12p; C_0603_1608Metric; LCSC Part Number C38523
C160, C161: 100n; C_0603_1608Metric; LCSC Part Number C14663
FB2, FB3: FerriteBead_Small; R_0603_1608Metric; LCSC Part Number C108301
R49: 2.49K 1%; R_0603_1608Metric; LCSC Part Number C227773
R113, R114, R115, R116, R117, R119, R121, R122, R123, R125, R128, R129, R130, R131, R133, R135, R136: 4K7 DNP; R_0603_1608Metric_Pad0.98x0.95mm_HandSolder; LCSC Part Number C99782; not fitted
R118, R120, R124, R126, R127, R132, R134: 4K7; R_0603_1608Metric_Pad0.98x0.95mm_HandSolder; LCSC Part Number C99782
U19: RTL8370N; LQFP-128_14x20mm_P0.5mm; LCSC Part Number C2803243
Y1: 25MHZ; Crystal_SMD_3225-4Pin_3.2x2.5mm; LCSC Part Number C9006

Connections:
+1.1V: C40.1, C42.1, C44.1, C46.1, C51.1, C52.1, C68.1, C71.1, C80.1, C81.1, C90.1, C92.1, C93.1, C94.1, C160.1, C161.1, FB2.1, FB3.1, U19.10 (AVDDL), U19.18 (AVDDL), U19.20 (DVDDL), U19.21 (DVDDL), U19.22 (DVDDL), U19.23 (DVDDL), U19.29 (AVDDL), U19.39 (AVDDL), U19.49 (AVDDL), U19.59 (AVDDL), U19.76 (DVDDL), U19.78 (DVDDL), U19.92 (DVDDL), U19.95 (DVDDL), U19.107 (AVDDL), U19.117 (AVDDL), U19.128 (AVDDL)
+3.3V: C39.1, C41.1, C43.1, C45.1, C47.1, C75.1, C76.1, C85.1, C91.1, C95.1, C96.1, R113.1, R115.1, R117.1, R119.1, R120.1, R121.1, R122.1, R123.1, R124.1, R125.1, R126.1, R127.1, U19.5 (AVDDH), U19.15 (AVDDH), U19.19 (AVDDH), U19.24 (AVDDH), U19.34 (AVDDH), U19.54 (AVDDH), U19.64 (AVDDH), U19.77 (DVDDIO), U19.96 (AVDDH), U19.102 (AVDDH), U19.112 (AVDDH)
EP5.AN: U19.7 (P3MDIAN)
EP5.AP: U19.6 (P3MDIAP)
EP5.BN: U19.9 (P3MDIBN)
EP5.BP: U19.8 (P3MDIBP)
EP5.CN: U19.12 (P3MDICN)
EP5.CP: U19.11 (P3MDICP)
EP5.DN: U19.14 (P3MDIDN)
EP5.DP: U19.13 (P3MDIDP)
EP6.AN: U19.26 (P4MDIAN)
EP6.AP: U19.25 (P4MDIAP)
EP6.BN: U19.28 (P4MDIBN)
EP6.BP: U19.27 (P4MDIBP)
EP6.CN: U19.31 (P4MDICN)
EP6.CP: U19.30 (P4MDICP)
EP6.DN: U19.33 (P4MDIDN)
EP6.DP: U19.32 (P4MDIDP)
ES0_0N: U19.104 (P0MDIAN)
ES0_0P: U19.103 (P0MDIAP)
ES0_1N: U19.106 (P0MDIBN)
ES0_1P: U19.105 (P0MDIBP)
ES0_2N: U19.109 (P0MDICN)
ES0_2P: U19.108 (P0MDICP)
ES0_3N: U19.111 (P0MDIDN)
ES0_3P: U19.110 (P0MDIDP)
ES0_L0: R119.2, R128.1, U19.94 (P0LED0)
ES0_L1: U19.93 (P0LED1)
ES1_0N: U19.114 (P1MDIAN)
ES1_0P: U19.113 (P1MDIAP)
ES1_1N: U19.116 (P1MDIBN)
ES1_1P: U19.115 (P1MDIBP)
ES1_2N: U19.119 (P1MDICN)
ES1_2P: U19.118 (P1MDICP)
ES1_3N: U19.121 (P1MDIDN)
ES1_3P: U19.120 (P1MDIDP)
ES1_L0: R121.2, R130.1, U19.89 (P1LED0)
ES1_L1: R126.2, R135.1, U19.90 (P1LED1)
ES2_0N: U19.125 (P2MDIAN)
ES2_0P: U19.124 (P2MDIAP)
ES2_1N: U19.127 (P2MDIBN)
ES2_1P: U19.126 (P2MDIBP)
ES2_2N: U19.2 (P2MDICN)
ES2_2P: U19.1 (P2MDICP)
ES2_3N: U19.4 (P2MDIDN)
ES2_3P: U19.3 (P2MDIDP)
ES2_L0: R123.2, R132.1, U19.86 (P2LED0)
ES2_L1: U19.87 (P2LED1)
ES3_0N: U19.36 (P5MDIAN)
ES3_0P: U19.35 (P5MDIAP)
ES3_1N: U19.38 (P5MDIBN)
ES3_1P: U19.37 (P5MDIBP)
ES3_2N: U19.41 (P5MDICN)
ES3_2P: U19.40 (P5MDICP)
ES3_3N: U19.43 (P5MDIDN)
ES3_3P: U19.42 (P5MDIDP)
ES3_L0: U19.74 (P5LED0)
ES3_L1: U19.75 (P5LED1)
ES4_0N: U19.46 (P6MDIAN)
ES4_0P: U19.45 (P6MDIAP)
ES4_1N: U19.48 (P6MDIBN)
ES4_1P: U19.47 (P6MDIBP)
ES4_2N: U19.51 (P6MDICN)
ES4_2P: U19.50 (P6MDICP)
ES4_3N: U19.53 (P6MDIDN)
ES4_3P: U19.52 (P6MDIDP)
ES4_L0: U19.72 (P6LED1)
ES4_L1: R115.2, R116.1, U19.71 (P6LED0)
ES6_0N: U19.56 (P7MDIAN)
ES6_0P: U19.55 (P7MDIAP)
ES6_1N: U19.58 (P7MDIBN)
ES6_1P: U19.57 (P7MDIBP)
ES6_2N: U19.61 (P7MDICN)
ES6_2P: U19.60 (P7MDICP)
ES6_3N: U19.63 (P7MDIDN)
ES6_3P: U19.62 (P7MDIDP)
ES6_L0: R113.2, R114.1, U19.68 (P7LED0)
ES6_L1: U19.69 (P7LED1)
GND: C39.2, C40.2, C41.2, C42.2, C43.2, C44.2, C45.2, C46.2, C47.2, C51.2, C52.2, C59.2, C60.2, C68.2, C71.2, C75.2, C76.2, C80.2, C81.2, C85.2, C90.2, C91.2, C92.2, C93.2, C94.2, C95.2, C96.2, C102.2, C103.2, C160.2, C161.2, R49.1, R114.2, R116.2, R118.2, R128.2, R129.2, R130.2, R131.2, R132.2, R133.2, R134.2, R135.2, R136.2, U19.16 (AGND), U19.129 (EPAD), Y1.2, Y1.4
MDC: U19.100 (SCK/MDC)
MDIO: U19.101 (SDA/MDIO)
unnamed: R49.2, U19.17 (MDIREF)
P0L2: R120.2, R129.1, U19.91 (P0LED2)
P1L2: R122.2, R131.1, U19.88 (P1LED2)
P2L2: R124.2, R133.1, U19.85 (P2LED2)
P3L0: R125.2, R134.1, U19.84 (P3LED0)
P3L1: U19.82 (P3LED1)
P3L2: R127.2, R136.1, U19.83 (P3LED2)
P4L0: R117.2, R118.1, U19.80 (P4LED0)
P4L1: U19.81 (P4LED1)
P4L2: U19.79 (P4LED2)
P5L2: U19.73 (P5LED2)
P6L2: U19.70 (P6LED2)
P7L2: U19.67 (P7LED2)
PLL0: C60.1, FB2.2, U19.122 (PLLVDDL0)
PLL1: C59.1, FB3.2, U19.44 (PLLVDDL1)
RST_N: U19.99 (nRESET)
XI: C102.1, U19.97 (XTAL0), Y1.3
XO: C103.1, U19.98 (XTAL1), Y1.1

Notes on the sheet:
Strapping for RTL8370N: 0=4k7ohm to GND, 1=4k7ohm to 3v3 : 470ohm LED limiting R P2LED0=0,P2LED2=1,P3LED0=0,P4LED0=0: eeProm Load Configuration P3LED2=1: Enable LED Power On Light P0LED2=1: Enable Embedded Phy P1LED1=1: Enable MAC/PHY EEE
Current @moderate @maximum trk ----- ------- ------ ---- 3.3v 55ma 400ma 0.2 1.0v 280ma 1300ma 0.5
