rickcox/Hepta-Pi/enet_sw_100m_detail.kicad_sch

## KiCad design enet_sw_100m_detail.kicad_sch (2023-05-14)

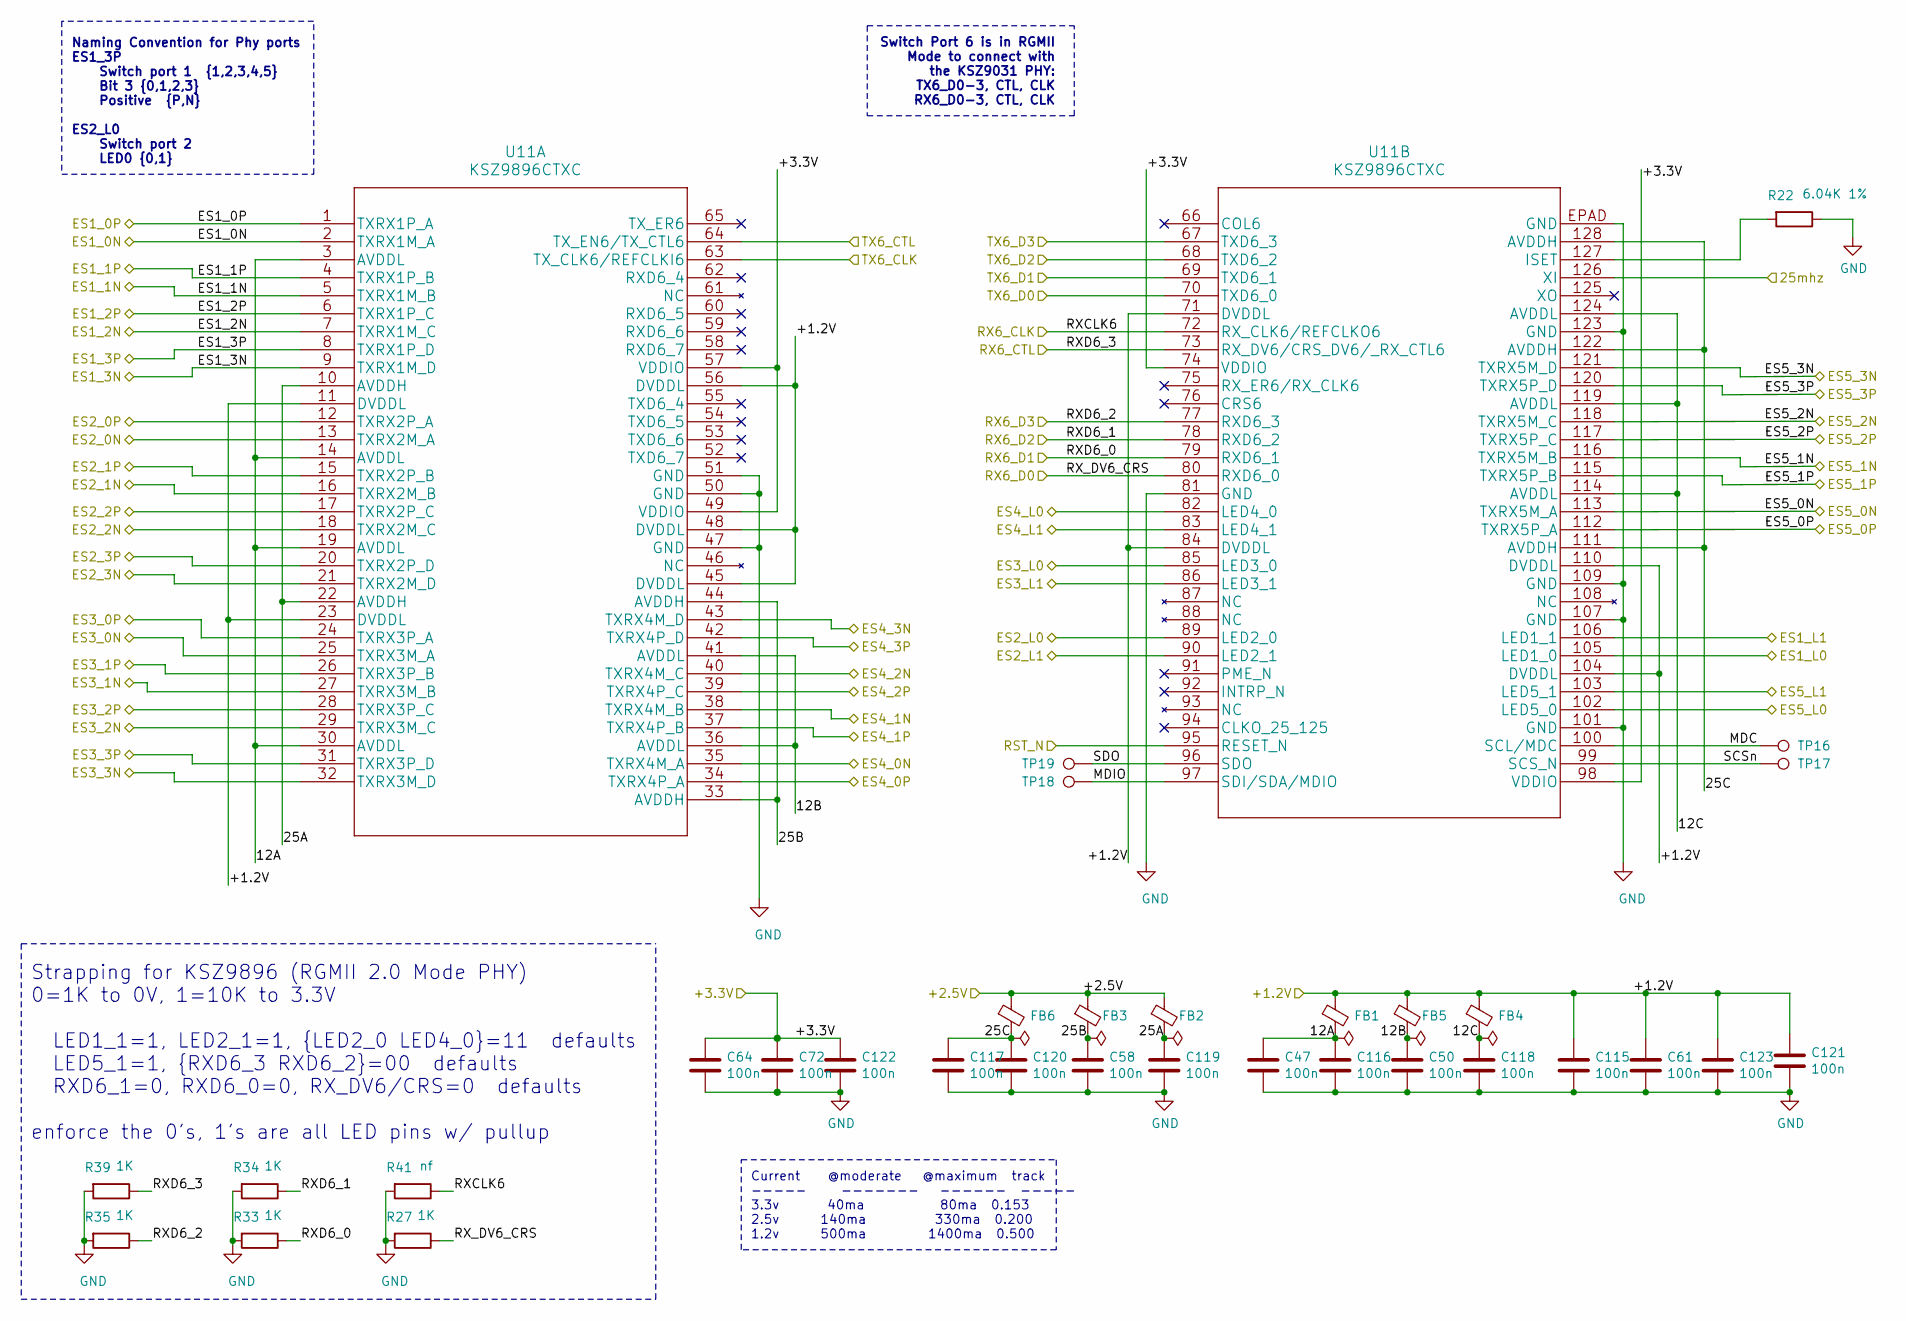
[picture p30: schematic enet_sw_100m_detail.kicad_sch]

Parts:
C47, C50, C58, C61, C64, C72, C115, C116, C117, C118, C119, C120, C121, C122, C123: 100n; C_0603_1608Metric; Part Description CAP CER 0.1UF 6.3V X5R 0603; LCSC Part Number C14663
FB1, FB2, FB3, FB4, FB5, FB6: FerriteBead_Small; R_0603_1608Metric; Manuf Partno BBPY00160808300Y00; LCSC Part Number C85831
R22: 6.04K 1%; R_0603_1608Metric; Part Description RES 6.04K M1005 1% 63mW 0603; LCSC Part Number C131439
R27, R33, R34, R35, R39: 1K; R_0603_1608Metric; Part Description RES 1K OHM 1% 1/10W 0603; LCSC Part Number C21190
R41: nf; R_0603_1608Metric_Pad0.98x0.95mm_HandSolder; Manuf Partno nf; LCSC Part Number nf
TP16, TP17, TP18, TP19: TestPoint; TestPoint_Pad_1.5x1.5mm; Manuf Partno nf; LCSC Part Number nf
U11: KSZ9896CTXC; TQFP128_EP_TX_MCH; Manuf Partno KSZ9896CTXC; LCSC Part Number C638296

Connections:
12A: C47.1, C116.1, FB1.2, U11.3 (AVDDL), U11.14 (AVDDL), U11.19 (AVDDL), U11.30 (AVDDL)
12B: C50.1, FB5.2, U11.36 (AVDDL), U11.41 (AVDDL)
12C: C118.1, FB4.2, U11.114 (AVDDL), U11.119 (AVDDL), U11.124 (AVDDL)
25A: C119.1, FB2.2, U11.10 (AVDDH), U11.22 (AVDDH)
25B: C58.1, FB3.2, U11.33 (AVDDH), U11.44 (AVDDH)
25C: C117.1, C120.1, FB6.2, U11.111 (AVDDH), U11.122 (AVDDH), U11.128 (AVDDH)
25mhz: U11.126 (XI)
+1.2V: C61.1, C115.1, C121.1, C123.1, FB1.1, FB4.1, FB5.1, U11.11 (DVDDL), U11.23 (DVDDL), U11.45 (DVDDL), U11.48 (DVDDL), U11.56 (DVDDL), U11.71 (DVDDL), U11.84 (DVDDL), U11.104 (DVDDL), U11.110 (DVDDL)
+2.5V: FB2.1, FB3.1, FB6.1
+3.3V: C64.1, C72.1, C122.1, U11.49 (VDDIO), U11.57 (VDDIO), U11.74 (VDDIO), U11.98 (VDDIO)
ES1_0N: U11.2 (TXRX1M_A)
ES1_0P: U11.1 (TXRX1P_A)
ES1_1N: U11.5 (TXRX1M_B)
ES1_1P: U11.4 (TXRX1P_B)
ES1_2N: U11.7 (TXRX1M_C)
ES1_2P: U11.6 (TXRX1P_C)
ES1_3N: U11.9 (TXRX1M_D)
ES1_3P: U11.8 (TXRX1P_D)
ES1_L0: U11.105 (LED1_0)
ES1_L1: U11.106 (LED1_1)
ES2_0N: U11.13 (TXRX2M_A)
ES2_0P: U11.12 (TXRX2P_A)
ES2_1N: U11.16 (TXRX2M_B)
ES2_1P: U11.15 (TXRX2P_B)
ES2_2N: U11.18 (TXRX2M_C)
ES2_2P: U11.17 (TXRX2P_C)
ES2_3N: U11.21 (TXRX2M_D)
ES2_3P: U11.20 (TXRX2P_D)
ES2_L0: U11.89 (LED2_0)
ES2_L1: U11.90 (LED2_1)
ES3_0N: U11.25 (TXRX3M_A)
ES3_0P: U11.24 (TXRX3P_A)
ES3_1N: U11.27 (TXRX3M_B)
ES3_1P: U11.26 (TXRX3P_B)
ES3_2N: U11.29 (TXRX3M_C)
ES3_2P: U11.28 (TXRX3P_C)
ES3_3N: U11.32 (TXRX3M_D)
ES3_3P: U11.31 (TXRX3P_D)
ES3_L0: U11.85 (LED3_0)
ES3_L1: U11.86 (LED3_1)
ES4_0N: U11.35 (TXRX4M_A)
ES4_0P: U11.34 (TXRX4P_A)
ES4_1N: U11.38 (TXRX4M_B)
ES4_1P: U11.37 (TXRX4P_B)
ES4_2N: U11.40 (TXRX4M_C)
ES4_2P: U11.39 (TXRX4P_C)
ES4_3N: U11.43 (TXRX4M_D)
ES4_3P: U11.42 (TXRX4P_D)
ES4_L0: U11.82 (LED4_0)
ES4_L1: U11.83 (LED4_1)
ES5_0N: U11.113 (TXRX5M_A)
ES5_0P: U11.112 (TXRX5P_A)
ES5_1N: U11.116 (TXRX5M_B)
ES5_1P: U11.115 (TXRX5P_B)
ES5_2N: U11.118 (TXRX5M_C)
ES5_2P: U11.117 (TXRX5P_C)
ES5_3N: U11.121 (TXRX5M_D)
ES5_3P: U11.120 (TXRX5P_D)
ES5_L0: U11.102 (LED5_0)
ES5_L1: U11.103 (LED5_1)
GND: C47.2, C50.2, C58.2, C61.2, C64.2, C72.2, C115.2, C116.2, C117.2, C118.2, C119.2, C120.2, C121.2, C122.2, C123.2, R22.1, R27.2, R33.2, R34.2, R35.2, R39.2, R41.2, U11.47 (GND), U11.50 (GND), U11.51 (GND), U11.81 (GND), U11.101 (GND), U11.107 (GND), U11.109 (GND), U11.123 (GND), U11.EPAD (GND)
MDC: TP16.1, U11.100 (SCL/MDC)
MDIO: TP18.1, U11.97 (SDI/SDA/MDIO)
unnamed: R22.2, U11.127 (ISET)
RST_N: U11.95 (RESET_N)
RX6_CLK: R41.1, U11.72 (RX_CLK6/REFCLKO6)
RX6_CTL: R39.1, U11.73 (RX_DV6/CRS_DV6/_RX_CTL6)
RX6_D0: R27.1, U11.80 (RXD6_0)
RX6_D1: R33.1, U11.79 (RXD6_1)
RX6_D2: R34.1, U11.78 (RXD6_2)
RX6_D3: R35.1, U11.77 (RXD6_3)
SCSn: TP17.1, U11.99 (SCS_N)
SDO: TP19.1, U11.96 (SDO)
TX6_CLK: U11.63 (TX_CLK6/REFCLKI6)
TX6_CTL: U11.64 (TX_EN6/TX_CTL6)
TX6_D0: U11.70 (TXD6_0)
TX6_D1: U11.69 (TXD6_1)
TX6_D2: U11.68 (TXD6_2)
TX6_D3: U11.67 (TXD6_3)

Notes on the sheet:
Strapping for KSZ9896 (RGMII 2.0 Mode PHY) 0=1K to 0V, 1=10K to 3.3V LED1_1=1, LED2_1=1, {LED2_0 LED4_0}=11 defaults LED5_1=1, {RXD6_3 RXD6_2}=00 defaults RXD6_1=0, RXD6_0=0, RX_DV6/CRS=0 defaults enforce the 0's, 1's are all LED pins w/ pullup
Naming Convention for Phy ports ES1_3P Switch port 1 {1,2,3,4,5} Bit 3 {0,1,2,3} Positive {P,N} ES2_L0 Switch port 2 LED0 {0,1}
Current @moderate @maximum track ----- ------- ------ ----- 3.3v 40ma 80ma 0.153 2.5v 140ma 330ma 0.200 1.2v 500ma 1400ma 0.500
Switch Port 6 is in RGMII Mode to connect with the KSZ9031 PHY: TX6_D0-3, CTL, CLK RX6_D0-3, CTL, CLK
