rickcox/Hepta-Pi/full_cm.kicad_sch

## KiCad design full_cm.kicad_sch (2023-05-14)

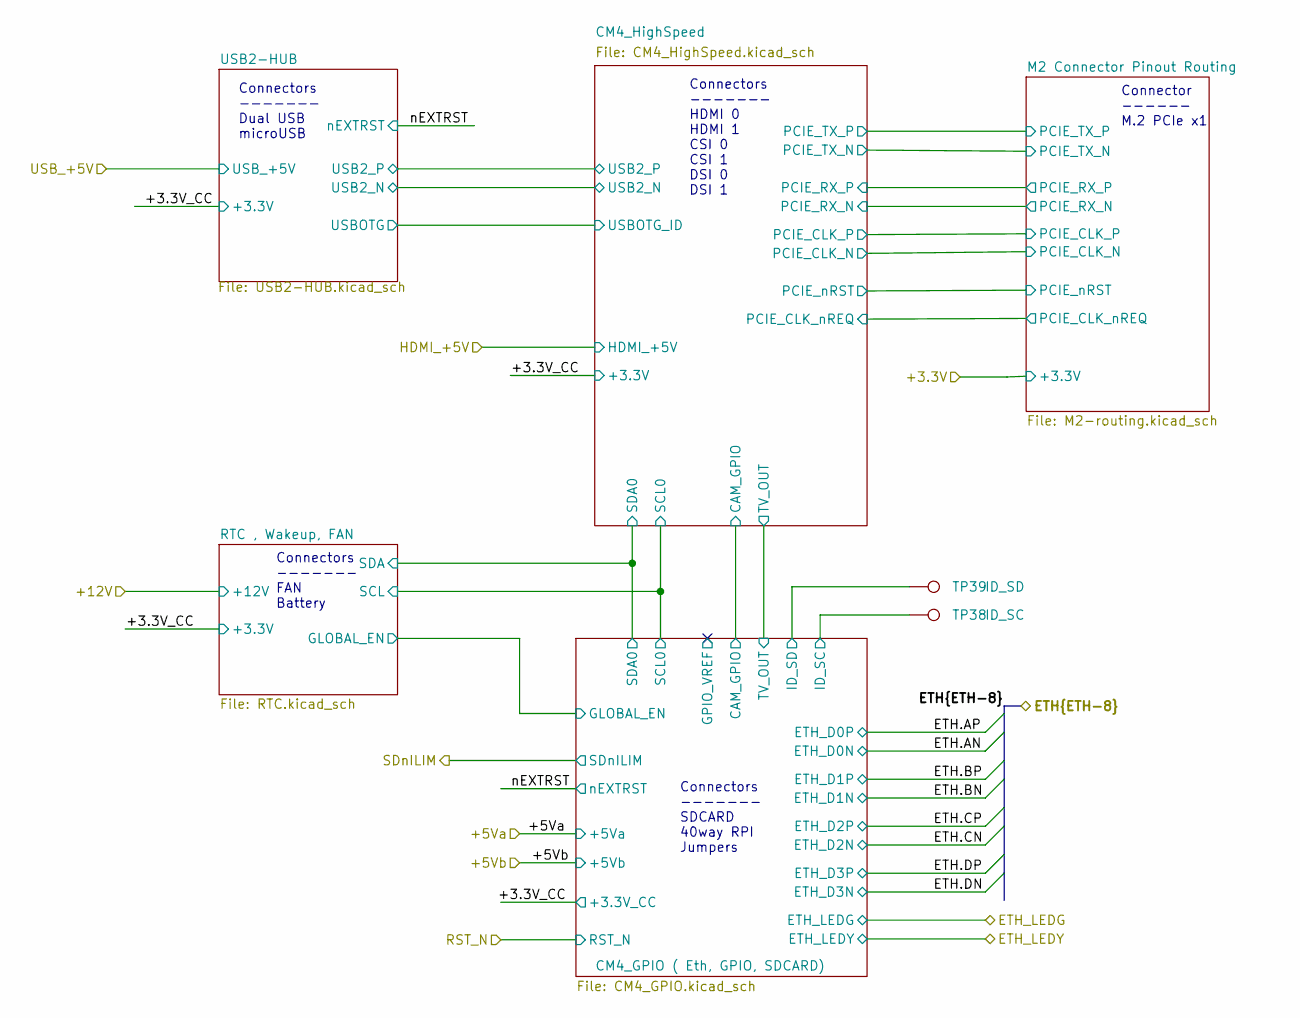
[picture p31: schematic full_cm.kicad_sch]

Parts:
TP38: ID_SC; TestPoint_Pad_D1.0mm; LCSC Part Number DNP
TP39: ID_SD; TestPoint_Pad_D1.0mm; LCSC Part Number DNP

Connections:
ID_SC: TP38.1
ID_SD: TP39.1

Notes on the sheet:
Connector ------ M.2 PCIe x1
Connectors ------- Dual USB microUSB
Connectors ------- SDCARD 40way RPI Jumpers
Connectors ------- FAN Battery
Connectors ------- HDMI 0 HDMI 1 CSI 0 CSI 1 DSI 0 DSI 1
