rickcox/Hepta-Pi/power.kicad_sch

## KiCad design power.kicad_sch (2023-05-14)

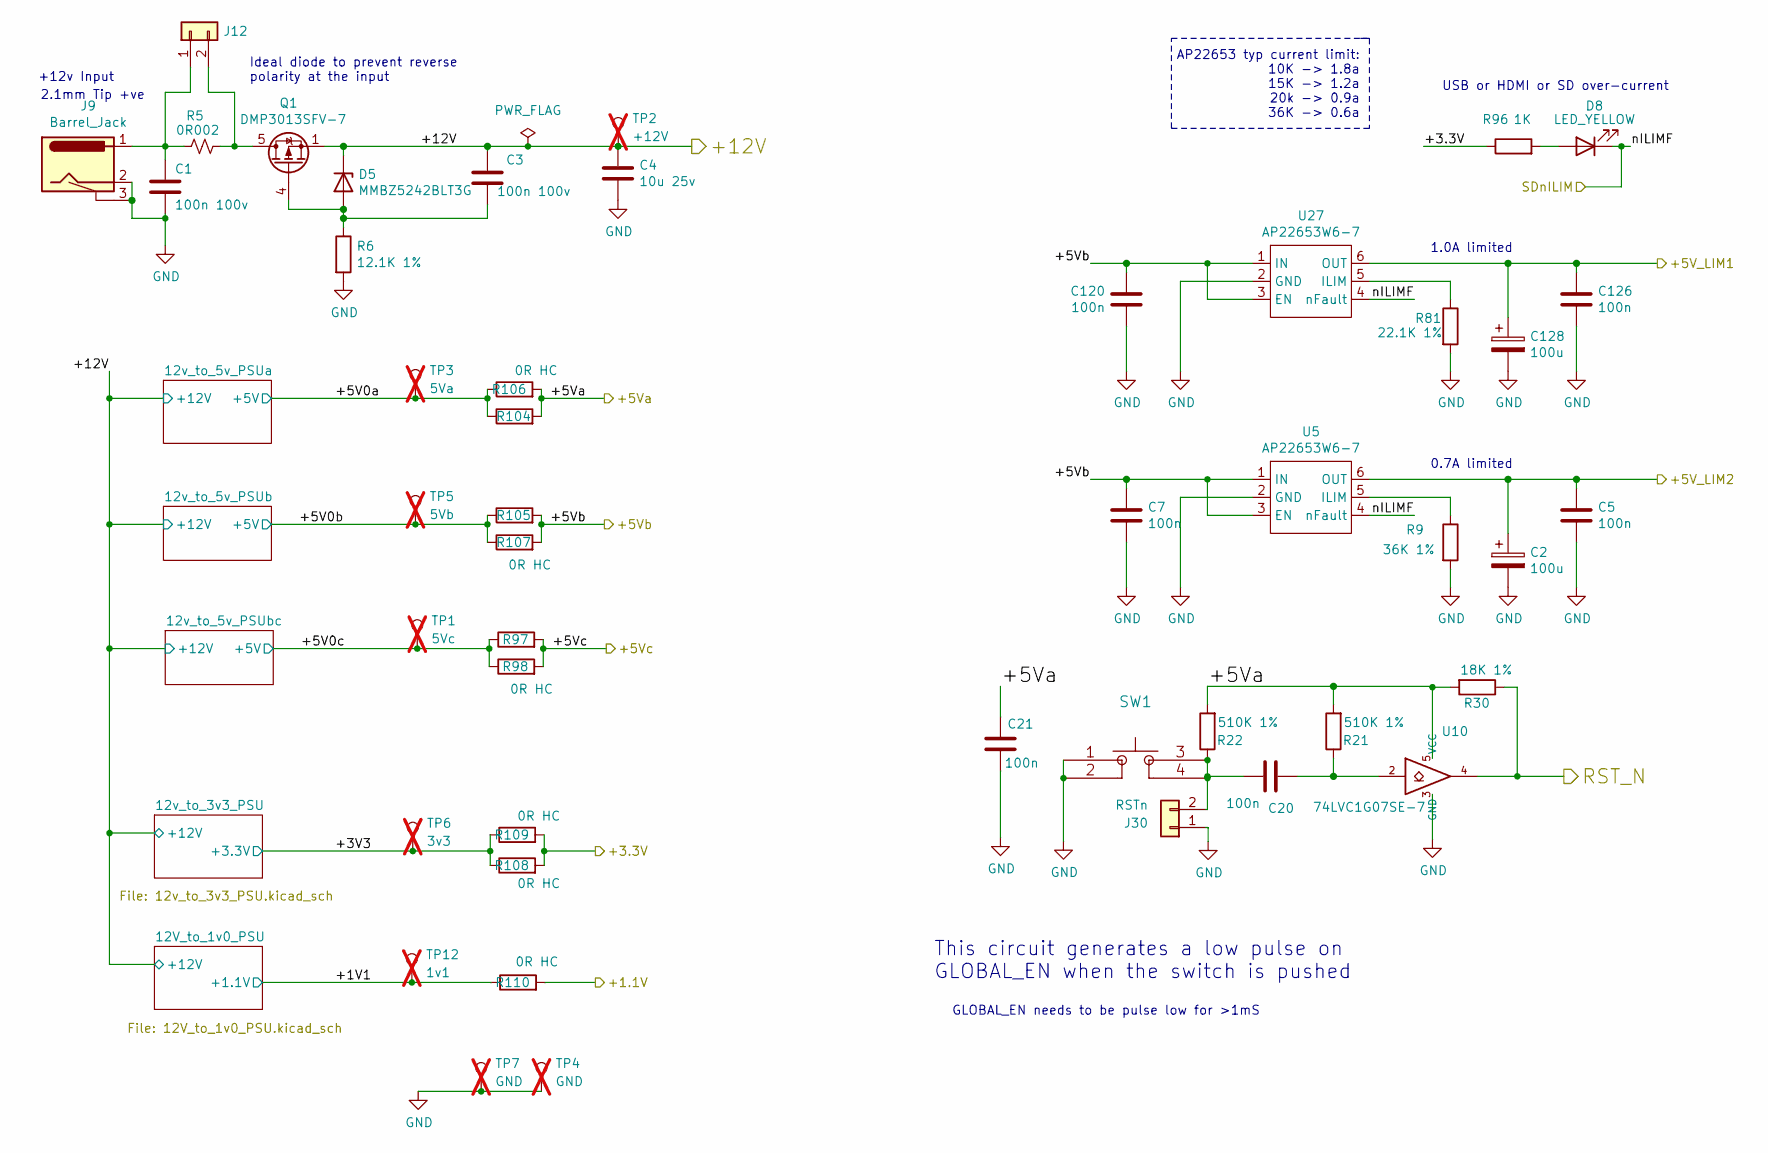
[picture p32: schematic power.kicad_sch]

Parts:
C1, C3: 100n 100v; C_0805_2012Metric; LCSC Part Number C28233
C2, C128: 100u; CP_EIA-3528-21_Kemet-B; LCSC Part Number C16133
C4: 10u 25v; C_0805_2012Metric; LCSC Part Number C440198
C5, C7, C20, C21, C120, C126: 100n; C_0402_1005Metric; LCSC Part Number C1525
D5: MMBZ5242BLT3G; D_SOT-23_ANK; LCSC Part Number C112551
D8: LED_YELLOW; LED_0805_2012Metric_Pad1.15x1.40mm_HandSolder; LCSC Part Number C2296
J9: Barrel_Jack; BarrelJack_Horizontal
J12: Conn_01x02; PinHeader_1x02_P2.54mm_Vertical
J30: RSTn; PinHeader_1x02_P2.54mm_Vertical
Q1: DMP3013SFV-7; Diodes_PowerDI3333-8; LCSC Part Number C264098
R5: 0R002; R_1206_3216Metric; LCSC Part Number C154630
R6: 12.1K 1%; R_0603_1608Metric; LCSC Part Number C22864
R9: 36K 1%; R_0603_1608Metric; LCSC Part Number C23147
R21, R22: 510K 1%; R_0603_1608Metric; LCSC Part Number C23192
R30: 18K 1%; R_0603_1608Metric; LCSC Part Number C25810
R81: 22.1K 1%; R_0603_1608Metric; LCSC Part Number C25961
R96: 1K; R_0603_1608Metric; LCSC Part Number C21190
R97, R98, R104, R105, R106, R107, R108, R109, R110: 0R HC; R_0805_2012Metric_Pad1.20x1.40mm_HandSolder; LCSC Part Number C1882631
SW1: pushButton-PTS647SM38SMTR2LFS; Part Description Tact Sw SPST-NO Top Actuated SMT 4.5mmX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; LCSC Part Number C2689502
TP1: 5Vc; TestPoint_THT_D1.6mm_Drill1.0mm; LCSC Part Number DNP; not fitted
TP2: +12V; TestPoint_THT_D1.6mm_Drill1.0mm; LCSC Part Number DNP; not fitted
TP3: 5Va; TestPoint_THT_D1.6mm_Drill1.0mm; LCSC Part Number DNP; not fitted
TP4, TP7: GND; TestPoint_THT_D1.6mm_Drill1.0mm; LCSC Part Number DNP; not fitted
TP5: 5Vb; TestPoint_THT_D1.6mm_Drill1.0mm; LCSC Part Number DNP; not fitted
TP6: 3v3; TestPoint_THT_D1.6mm_Drill1.0mm; LCSC Part Number DNP; not fitted
TP12: 1v1; TestPoint_THT_D1.6mm_Drill1.0mm; LCSC Part Number DNP; not fitted
U5, U27: AP22653W6-7; SOT-23-6; LCSC Part Number C2158037
U10: 74LVC1G07SE-7; SOT-353_SC-70-5; LCSC Part Number C67531

Connections:
+1.1V: R110.2
+1V1: R110.1, TP12.1
+3.3V: R96.1, R108.2, R109.2
+3V3: R108.1, R109.1, TP6.1
+5V0a: R104.1, R106.1, TP3.1
+5V0b: R105.1, R107.1, TP5.1
+5V0c: R97.1, R98.1, TP1.1
+5V_LIM1: C126.1, C128.1, U27.6 (OUT)
+5V_LIM2: C2.1, C5.1, U5.6 (OUT)
+5Va: C21.1, R21.2, R22.2, R30.2, R104.2, R106.2, U10.5 (VCC)
+5Vb: C7.1, C120.1, R105.2, R107.2, U5.1 (IN), U5.3 (EN), U27.1 (IN), U27.3 (EN)
+5Vc: R97.2, R98.2
+12V: C3.1, C4.1, D5.1 (K), Q1.1 (S), Q1.2 (S), Q1.3 (S), TP2.1
GND: C1.2, C2.2, C4.2, C5.2, C7.2, C21.2, C120.2, C126.2, C128.2, J9.2, J9.3, J30.1, R6.2, R9.2, R81.2, SW1.1, SW1.2, TP4.1, TP7.1, U5.2 (GND), U10.3 (GND), U27.2 (GND)
unnamed: C1.1, J9.1, J12.1, R5.1
unnamed: C3.2, D5.2 (A), Q1.4 (G), R6.1
unnamed: C20.1, R21.1, U10.2
unnamed: C20.2, J30.2, R22.1, SW1.3, SW1.4
unnamed: D8.2 (A), R96.2
unnamed: J12.2, Q1.5 (D), R5.2
unnamed: R9.1, U5.5 (ILIM)
unnamed: R81.1, U27.5 (ILIM)
RST_N: R30.1, U10.4
nILIMF: D8.1 (K), U5.4 (nFault), U27.4 (nFault)

Notes on the sheet:
+12v Input
AP22653 typ current limit: 10K -> 1.8a 15K -> 1.2a 20k -> 0.9a 36K -> 0.6a
USB or HDMI or SD over-current
GLOBAL_EN needs to be pulse low for >1mS
0.7A limited
Ideal diode to prevent reverse polarity at the input
1.0A limited
This circuit generates a low pulse on GLOBAL_EN when the switch is pushed
2.1mm Tip +ve
