rickcox/Hepta-Pi/tiny-cm.kicad_sch

## KiCad design tiny-cm.kicad_sch (2023-05-14)

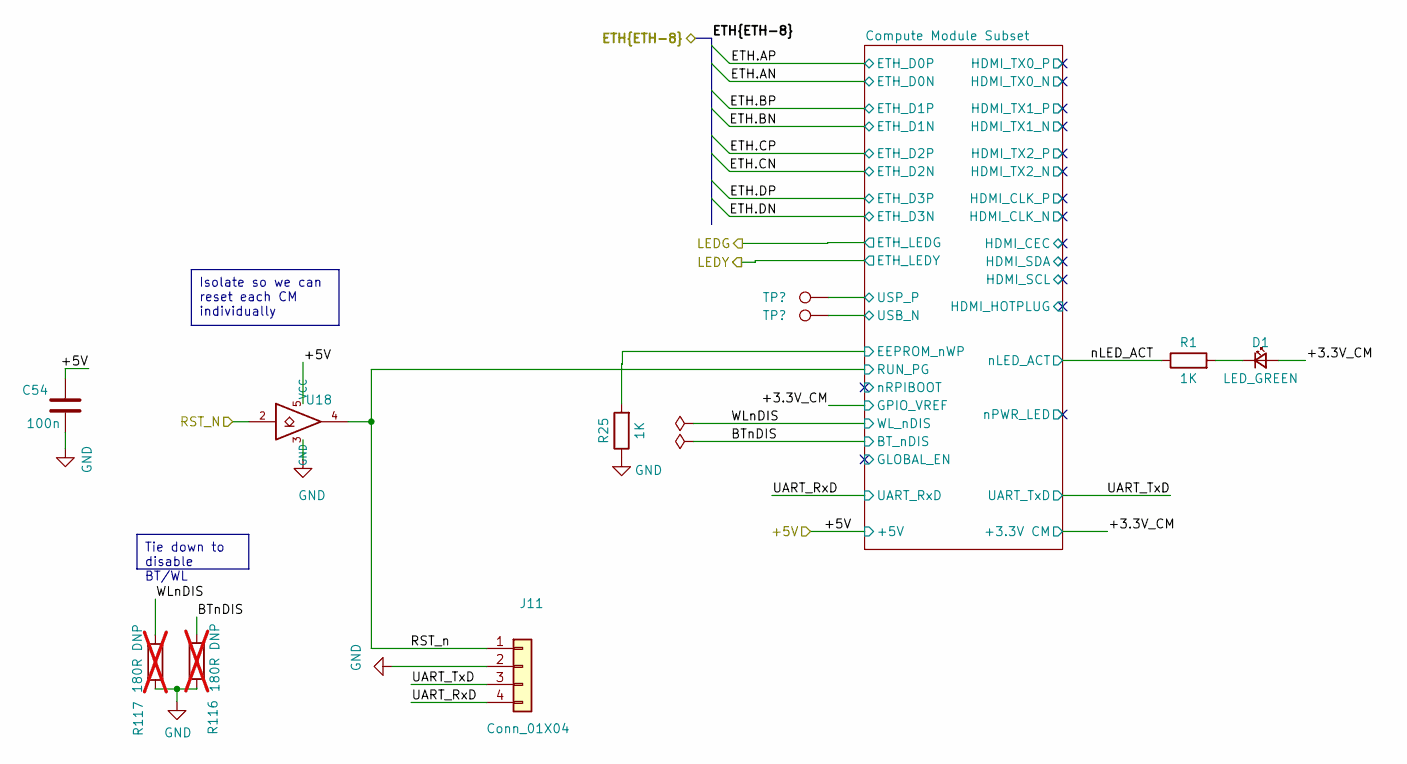
[picture p33: schematic tiny-cm.kicad_sch]

Parts:
C54: 100n; C_0402_1005Metric; LCSC Part Number C1525
D1: LED_GREEN; LED_0805_2012Metric_Pad1.15x1.40mm_HandSolder; LCSC Part Number C2297
J11: Conn_01X04; PinHeader_1x04_P2.54mm_Vertical
R1, R25: 1K; R_0603_1608Metric; LCSC Part Number C21190
R116, R117: 180R DNP; R_0603_1608Metric_Pad0.98x0.95mm_HandSolder; LCSC Part Number DNP; not fitted
TP16, TP17: TestPoint; TestPoint_Pad_D1.0mm; LCSC Part Number DNP
U18: 74LVC1G07SE-7; SOT-353_SC-70-5; LCSC Part Number C67531

Connections:
+3.3V_CM: D1.2 (A)
+5V: C54.1, U18.5 (VCC)
BTnDIS: R116.2
EEPROM_nWP: R25.2
GND: C54.2, J11.2, R25.1, R116.1, R117.1, U18.3 (GND)
unnamed: D1.1 (K), R1.2
RST_N: J11.1, U18.2, U18.4
UART_RxD: J11.4
UART_TxD: J11.3
USB_N: TP16.1
USP_P: TP17.1
WLnDIS: R117.2
nLED_ACT: R1.1

Notes on the sheet:
Tie down to disable BT/WL
Isolate so we can reset each CM individually
